kpbianco/gr86-cca-telemetry/docs/engineering/rvb22/analyses/mated_i22/MATED_SERVICE_ENVELOPES.png

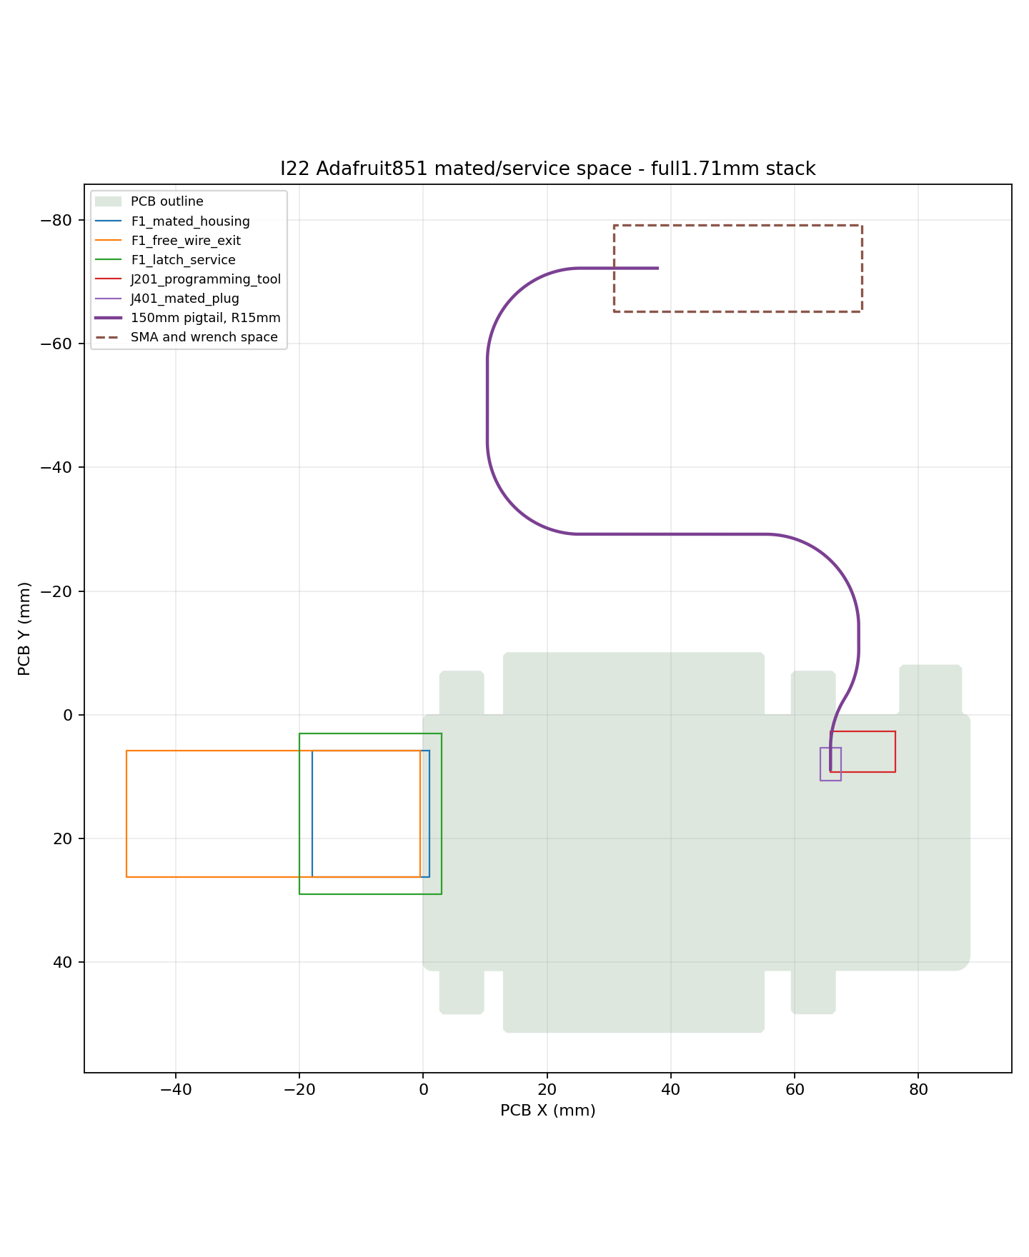
docs/engineering/rvb22/analyses/mated_i22/MATED_SERVICE_ENVELOPES.png
