kpbianco/gr86-cca-telemetry/docs/engineering/rvb22/candidate/cad/models/ENVELOPE_TI_DRB0008J_TCAN3403.step

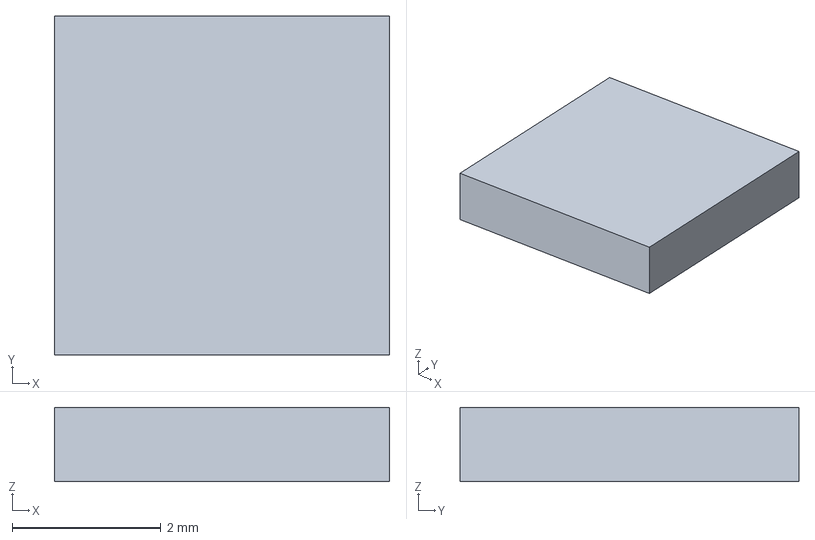
[picture p22: CAD file, 2026-09-10]
docs/engineering/rvb22/candidate/cad/models/ENVELOPE_TI_DRB0008J_TCAN3403.step
4.50 x 4.55 x 1.00 mm
