kpbianco/gr86-cca-telemetry/docs/engineering/rvb22/candidate/cad/models/ENVELOPE_TPS3808_DBV0006A.step

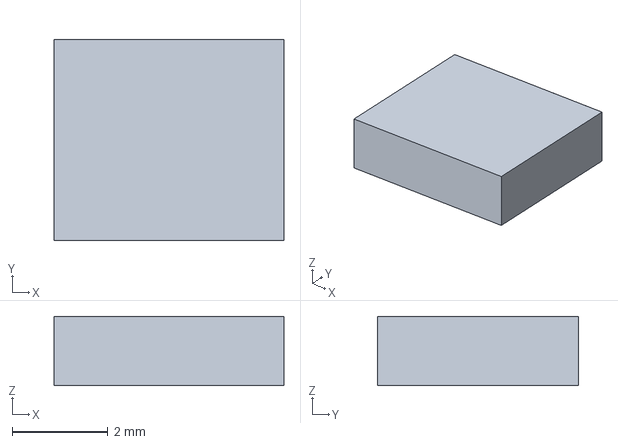
[picture p23: CAD file, 2026-09-10]
docs/engineering/rvb22/candidate/cad/models/ENVELOPE_TPS3808_DBV0006A.step
4.80 x 4.20 x 1.45 mm
