kpbianco/gr86-cca-telemetry/docs/engineering/rvb22/candidate/cad/models/ENVELOPE_TI_DDA0008B_4214849B.step

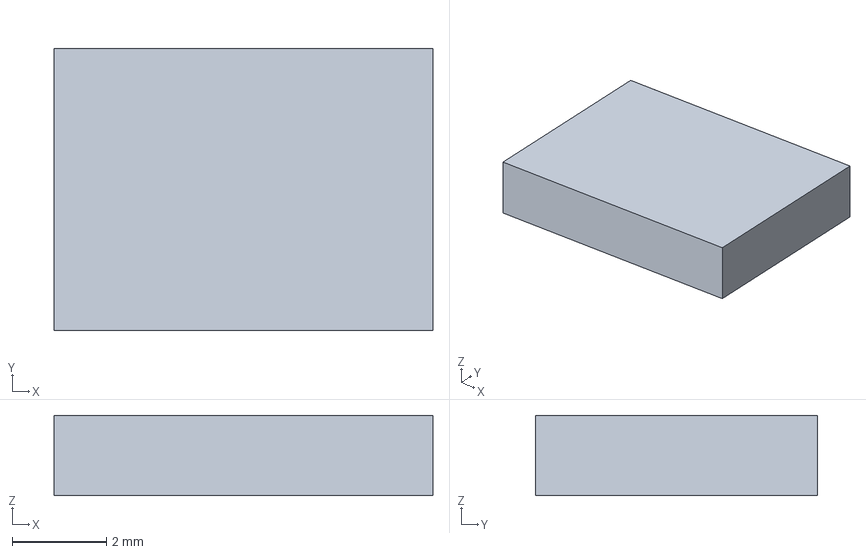
[picture p24: CAD file, 2026-09-10]
docs/engineering/rvb22/candidate/cad/models/ENVELOPE_TI_DDA0008B_4214849B.step
8.05 x 6.00 x 1.70 mm
