kpbianco/gr86-cca-telemetry/docs/engineering/rvb22/candidate/cad/models/ENVELOPE_WSLP0603_MANUFACTURER.step

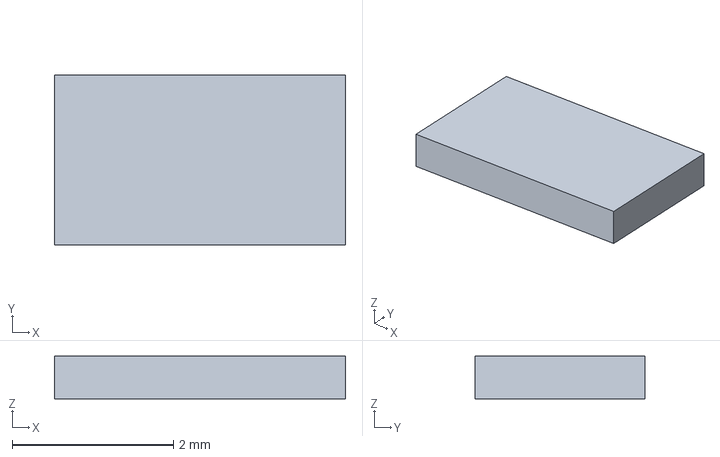
[picture p25: CAD file, 2026-09-10]
docs/engineering/rvb22/candidate/cad/models/ENVELOPE_WSLP0603_MANUFACTURER.step
3.61 x 2.11 x 0.533 mm
