kpbianco/gr86-cca-telemetry/docs/engineering/rvb22/candidate/mechanics/HARNESS_CORRIDORS_C03.scad

// Service and installed harness envelopes only; translucent volumes are not fabricated parts.
// Primary left: preserve twist, maximum6mm round bundle,≤1.3mmstrap; maxstack7.3mm.
color([0,0.4,1,.2])translate([-7.5,25,-16.3])cube([7,17,7.3]);
// Side parked T18R head volumes; do not put3.7mmheads beneath6mmbundle.
for(y=[31,37])color([0,0.8,1,.3])translate([-12.5,y-2.6,-12.9])cube([5.2,5.2,3.9]);
// Right coax service loop only; SMA bulkhead carries external coax pull.
for(y=[33,39]){
 color([0,.4,1,.2])translate([60.55,y-.8,-11.8])cube([3.9,1.6,2.8]);
 color([0,.8,1,.3])translate([59.9,y-2.6,-12.9])cube([5.2,5.2,3.9]);
}
