kpbianco/gr86-cca-telemetry/docs/engineering/rvb22/candidate/mechanics/MECH_GEOMETRY.scad

mounts=[[6.2, -4], [63, -4], [6.2, 45.28735489815251], [63, 45.263840607765246]];
outline=[[0.0, 0.980947], [0.0007564188822328788, 0.942435158452663], [0.003024212185312014, 0.9039827044031863], [0.006799883183623678, 0.8656489279468407], [0.01207761014488229, 0.8274929361891232], [0.018849255306698454, 0.78957356210812], [0.027104377424249204, 0.7519492738395437], [0.03683024786970257, 0.7146780845243252], [0.04801187025857423, 0.6778174628577655], [0.060632003572752335, 0.6414242444781693], [0.0746711887445386, 0.6055545443315986], [0.09010777866071418, 0.5702636701478605], [0.10691797154036797, 0.5356060371611512], [0.12507584763502144, 0.5016350842068436], [0.1445534091944619, 0.46840319132378905], [0.16532062363665956, 0.43596159898918896], [0.18734546985520617, 0.4043603291105594], [0.21059398759287262, 0.37364810789661906], [0.23503032980515604, 0.3438722907260233], [0.260616817933077, 0.3150787891297888], [0.287314, 0.287312], [0.3150803908230424, 0.26061490483005567], [0.3438735029496004, 0.23502850133291553], [0.3736489390329585, 0.21059224229236606], [0.4043607870385453, 0.1873438070346387], [0.43596169103768645, 0.16531904332902592], [0.468402924227763, 0.14455191211265295], [0.5016344640661801, 0.12507443512463678], [0.53560506940229, 0.10691664553038094], [0.5702623594883429, 0.09010654161213605], [0.6055528947476301, 0.07467004359723661], [0.641422259175283, 0.06063095369057858], [0.6778151442446667, 0.04801091937296942], [0.7146754341899937, 0.03682940002194035], [0.7519462925336527, 0.027103636906487982], [0.7895702497248368, 0.018848626602015806], [0.8274892917543318, 0.012077097866464714], [0.8656449496088303, 0.006799492013290109], [0.903978389426835, 0.0030239468115478285], [0.9424305032171397, 0.0007562839379161579], [0.980942, 0.0], [2.7, 0.0], [2.7, -6.5], [3.2, -7.0], [9.2, -7.0], [9.7, -6.5], [9.7, 0.0], [13.0, 0.0], [13.0, -9.5], [13.5, -10.0], [54.5, -10.0], [55.0, -9.5], [55.0, 0.0], [59.5, 0.0], [59.5, -6.5], [60.0, -7.0], [66.0, -7.0], [66.5, -6.5], [66.5, 0.0], [87.273825, 0.0], [87.279325, 0.000119], [87.31917532744609, 0.0026236857404802194], [87.35889700611345, 0.006686971610978976], [87.39842910058384, 0.012302624289232122], [87.43771096627245, 0.019462029029937433], [87.47668234246028, 0.02815420288028525], [87.51528344473775, 0.038365811528462634], [87.55345505671744, 0.05008118975928022], [87.59113862087561, 0.06328236548554456], [87.62827632838292, 0.07794908731830896], [87.66481120778663, 0.09405885563370964], [87.70068721240811, 0.11158695708872601], [87.73584930632194, 0.1305065025329204], [87.7702435487841, 0.15078846825799386], [87.80381717698043, 0.17240174052188162], [87.83651868696788, 0.19531316327908455], [87.86829791268461, 0.21948758904401522], [87.89910610290771, 0.2448879328093322], [87.92889599604048, 0.2714752289365473], [87.95762189261458, 0.2992086909316338], [87.98523972539566, 0.32804577401393376], [88.01170712698514, 0.3579422403823842], [88.03698349481435, 0.38885222707893363], [88.06103005343128, 0.4207283163450509], [88.0838099139844, 0.4535216083633855], [88.10528813081234, 0.48718179627299796], [88.1254317550527, 0.5216572433430767], [88.14420988518748, 0.5568950621867558], [88.16159371444789, 0.5928411958935125], [88.1775565750056, 0.629440500955684], [88.19207397888283, 0.6666368318618888], [88.20512365551836, 0.7043731272275816], [88.21668558593187, 0.7425914973306122], [88.2267420334342, 0.781233312917503], [88.23527757083666, 0.8202392951442118], [88.242279104117, 0.8595496065134053], [88.24773589250667, 0.8991039426687403], [88.2516395649676, 0.9388416249053337], [88.25398413303402, 0.9787016932545063], [88.254766, 1.018623], [88.254766, 38.837428], [88.25282560831081, 38.93625815706814], [88.24700661399163, 39.03493593760223], [88.23731798971754, 39.13330918409585], [88.22377467499068, 39.23122620862289], [88.20639755310395, 39.3285360267347], [88.1852134189399, 39.425088590272594], [88.16025493765383, 39.520735018736566], [88.13156059430547, 39.61532782885354], [88.09917463451636, 39.70872116199118], [88.06314699624474, 39.800771009066494], [88.02353323278307, 39.89133543260258], [87.9803944270969, 39.98027478559096], [87.93379709763715, 40.06745192682213], [87.88381309577116, 40.15273243235229], [87.83051949499047, 40.235984802780095], [87.77399847206637, 40.31708066601388], [87.71433718033633, 40.39589497521674], [87.65162761531678, 40.47230620162411], [87.58596647284935, 40.546196521936665], [87.517455, 40.617452], [87.45586352761268, 40.67667108709577], [87.39199461067004, 40.733426449801584], [87.32594673031547, 40.787630575548256], [87.25782172749265, 40.83919988558521], [87.18772464591447, 40.88805486385268], [87.11576357009325, 40.93412017958964], [87.0420494586825, 40.97732480348823], [86.96669597338692, 41.0176021172157], [86.88981930370436, 41.05489001613497], [86.81153798777032, 41.08913100506534], [86.73197272958086, 41.12027228693585], [86.65124621287598, 41.14826584419443], [86.56948291197034, 41.1730685128474], [86.48680889982317, 41.194642049015215], [86.403351653643, 41.21295318790161], [86.3192398583273, 41.227973695085524], [86.23460320803983, 41.23968041005645], [86.14957220623191, 41.24805528192625], [86.0642779644157, 41.25308539726227], [85.978852, 41.254763], [84.927437, 41.254763], [66.5, 41.262391664], [66.5, 47.763840608], [66.0, 48.263840608], [60.0, 48.263840608], [59.5, 47.763840608], [59.5, 41.265289552], [55.0, 41.26715248], [55.0, 50.775846143], [54.5, 51.275846143], [13.5, 51.275846143], [13.0, 50.775846143], [13.0, 41.284539807], [9.7, 41.285905954], [9.7, 47.787354898], [9.2, 48.287354898], [3.2, 48.287354898], [2.7, 47.787354898], [2.7, 41.288803842], [2.557101, 41.288863], [1.475399, 41.288863], [1.4122104655346492, 41.28762231281473], [1.3491193576042668, 41.28390178964085], [1.2862229598747368, 41.277707167358635], [1.2236182557775235, 41.269047997798516], [1.1614017789655595, 41.25793763301257], [1.0996694644626723, 41.24439320468623], [1.03851650073607, 41.22843559772205], [0.9780371829199807, 41.21008941803605], [0.9183247674167766, 41.18938295461655], [0.8594713280997736, 41.16634813590377], [0.8015676143394357, 41.14102048055766], [0.7447029110719076, 41.113439042689656], [0.6889649011256369, 41.083646351643026], [0.634439530018376, 41.05168834641451], [0.5812108734330366, 41.01761430481844], [0.5293610075767512, 40.98147676750257], [0.47896988262303, 40.94333145693274], [0.4301151994321739, 40.90323719147131], [0.3828722897400214, 40.8612557946819], [0.337314, 40.817452], [0.305970845153, 40.78485295628958], [0.2759316730593214, 40.75104853133481], [0.24724280095893103, 40.716090847999034], [0.2199484640714049, 40.6800338073486], [0.19409074738987742, 40.64293300554305], [0.169709520790415, 40.60484564811171], [0.14684237755686635, 40.565830461748796], [0.1255245764159767, 40.52594760376301], [0.10578898717214313, 40.48525856932134], [0.08766604002564038, 40.44382609662996], [0.0711836786524549, 40.40171407019854], [0.05636731711807896, 40.35898742233705], [0.043239800691699415, 40.315712033036995], [0.03182137062119672, 40.271954628391356], [0.022129632923273412, 40.22778267771005], [0.01417953123683069, 40.183264289489316], [0.007983323781449947, 40.13846810639559], [0.003550564456509253, 40.09346319942575], [0.0008880881100770122, 40.04831896140691], [0.0, 40.003105], [0.0, 37.820272], [2e-06, 2.834492], [0.0, 0.980947]];
