kpbianco/gr86-cca-telemetry/docs/engineering/rvb22/candidate/mechanics/THERMAL_CONTACT_T01.scad

// T01 thermal correction candidate, PCB bottomZ0. Package/copper heat-flow execution gate remains.
$fn=64;
// Copper packet is a volume envelope only:40 unbonded C110 laminae, each0.050..0.055mm.
module foil_packet(){translate([0,28.8,0])rotate([90,0,0])linear_extrude(17)polygon(points=[[68.36742356920699, -2.327], [66.6, -2.327], [66.6, -0.127], [72.0, -0.127], [72.10781885436252, -0.13229680066058358], [72.21459935421774, -0.14813619155644653], [72.31931314497992, -0.17436563069457023], [72.4209517756016, -0.21073251423758466], [72.5185364105086, -0.2568866092168096], [72.61112725632157, -0.3123834264672003], [72.69783261258002, -0.3766885013009893], [72.7778174593052, -0.4491825406947978], [72.85031149869901, -0.52916738741999], [72.9146165735328, -0.6158727436784377], [72.9701133907832, -0.7084635894914025], [73.01626748576241, -0.8060482243984013], [73.05263436930542, -0.9076868550200916], [73.07886380844356, -1.012400645782259], [73.09470319933942, -1.1191811456374834], [73.1, -1.227], [73.09487815202365, -1.3330275069087165], [73.07956030505223, -1.438067637868891], [73.05418910578301, -1.5411422118219895], [73.01900082226263, -1.6412913518625305], [72.97432314365243, -1.7375824240446052], [72.92057212863925, -1.8291187224896746], [72.85824833090943, -1.9150478199160048], [72.78793213776713, -1.994569505825846], [72.71027836530604, -2.066943238426374], [72.62601016046679, -2.1314950408887503], [72.53591226676653, -2.187623777724227], [72.44082371641346, -2.234806752828848], [72.34163001686069, -2.2726045770652346], [72.23925490456152, -2.300665260052341], [72.13465174271914, -2.3187274880585806], [72.02879464313867, -2.326623057473113], [71.90058141754851, -2.32998043894255], [71.80143533452095, -2.3377834049017934], [71.70283350343949, -2.350764582230358], [71.60504618506926, -2.3688883904235123], [71.5083414076529, -2.3921051533827487], [71.41298423226331, -2.420351235574614], [71.31923602629023, -2.4535492164511146], [71.22735374704972, -2.4916081026542893], [71.13758923748254, -2.534423577422475], [71.05018853586998, -2.581878286515418], [70.96539120145998, -2.6338421598740327], [70.88342965785215, -2.69017276813329], [70.8045285559402, -2.750715713011612], [70.72890415816008, -2.8153050505054087], [70.6567637457299, -2.883763745729839], [70.58830505050534, -2.955904158160167], [70.52371571301163, -3.031528555940172], [70.4631727681333, -3.1104296578521233], [70.40684215987407, -3.1923912014599107], [70.35487828651533, -3.2771885358701187], [70.30742357742251, -3.3645892374824644], [70.26460810265428, -3.454353747049748], [70.22654921645118, -3.5462360262900696], [70.19335123557458, -3.639984232263409], [70.16510515338277, -3.735341407652838], [70.1418883904235, -3.8320461850692933], [70.12376458223035, -3.9298335034395655], [70.11078340490178, -4.028435334520958], [70.10298043894254, -4.127581417548563], [70.1, -4.241399788793378], [70.1, -9.227], [70.09962305747311, -9.25579464313863], [70.09551166173684, -9.412802511867461], [70.09249767137017, -9.470312874029457], [70.08017475321127, -9.626890395103587], [70.07415503361601, -9.684164201245066], [70.0536543692966, -9.839882206562798], [70.04464542010577, -9.896762473162042], [70.01602320052177, -10.051194150494627], [70.00404971463885, -10.107524972694822], [69.96738439130463, -10.260247035549106], [69.95247918722222, -10.315874014481835], [69.90787125724049, -10.466467862299114], [69.89007518908686, -10.521238528281998], [69.837646919693, -10.669291393793058], [69.81700876525404, -10.723055624237448], [69.75690385869025, -10.868161704828948], [69.73348018571265, -10.920772135716533], [69.66586338534995, -11.062533705707772], [69.63971839649325, -11.113846135504243], [69.56477503528146, -11.251874636285603], [69.53598039214282, -11.301748421187552], [69.45391588462577, -11.435665526232635], [69.4225505113205, -11.483963965662385], [69.33358979060907, -11.613402617494723], [69.2997396574452, -11.659993328787014], [69.20412655869127, -11.784598745059107], [69.16788444653096, -11.829354026312698], [69.06588103859224, -11.948784672239759], [69.0273462845457, -11.991581852339715], [68.91923215167316, -12.105510376822783], [68.87851037682276, -12.146232151673171], [68.76458185233969, -12.254346284545711], [68.72178467223976, -12.292881038592228], [68.6023540263127, -12.394884446530959], [68.55759874505911, -12.431126558691263], [68.43299332878702, -12.526739657445193], [68.38640261749475, -12.560589790609049], [68.25696396566242, -12.649550511320477], [68.20866552623262, -12.680915884625781], [68.07474842118754, -12.762980392142826], [68.02487463628556, -12.79177503528148], [67.8868461355042, -12.866718396493267], [67.83553370570775, -12.892863385349957], [67.6937721357165, -12.960480185712656], [67.64116170482902, -12.983903858690207], [67.49605562423753, -13.04400876525401], [67.44229139379304, -13.064646919693004], [67.29423852828198, -13.11707518908686], [67.23946786229916, -13.134871257240471], [67.08887401448189, -13.179479187222215], [67.03324703554904, -13.194384391304654], [66.88052497269474, -13.231049714638866], [66.82419415049463, -13.243023200521767], [66.66976247316205, -13.271645420105763], [66.61288220656276, -13.280654369296604], [66.45716420124504, -13.301155033616011], [66.3998903951036, -13.30717475321126], [66.24331287402946, -13.319497671370163], [66.18580251186748, -13.322511661736836], [66.02879464313865, -13.326623057473114], [66.0, -13.327], [58.0, -13.327], [58.0, -11.127], [65.98560021120666, -11.127], [66.09941858245152, -11.12401956105745], [66.198564665479, -11.116216595098212], [66.29716649656054, -11.103235417769637], [66.39495381493076, -11.085111609576485], [66.49165859234711, -11.061894846617248], [66.58701576773667, -11.033648764425392], [66.68076397370979, -11.000450783548882], [66.77264625295031, -10.962391897345704], [66.8624107625175, -10.919576422577503], [66.94981146412995, -10.87212171348463], [67.03460879853999, -10.820157840125988], [67.11657034214791, -10.763827231866665], [67.19547144405982, -10.703284286988378], [67.27109584183987, -10.638694949494633], [67.34323625427007, -10.570236254270185], [67.41169494949473, -10.49809584183977], [67.47628428698836, -10.422471444059855], [67.5368272318667, -10.343570342147883], [67.59315784012593, -10.26160879854008], [67.64512171348467, -10.176811464129878], [67.69257642257753, -10.089410762517462], [67.73539189734565, -9.99964625295044], [67.77345078354887, -9.907763973709809], [67.8066487644254, -9.814015767736626], [67.83489484661723, -9.718658592347161], [67.8581116095765, -9.621953814930702], [67.87623541776965, -9.524166496560431], [67.88921659509822, -9.425564665479046], [67.89701956105746, -9.326418582451439], [67.9, -9.212600211206624], [67.9, -4.227], [67.90037694252689, -4.19820535686137], [67.90448833826316, -4.041197488132539], [67.90750232862983, -3.983687125970544], [67.91982524678873, -3.827109604896414], [67.92584496638399, -3.7698357987549334], [67.9463456307034, -3.6141177934372015], [67.95535457989423, -3.5572375268379597], [67.98397679947823, -3.402805849505375], [67.99595028536115, -3.346475027305181], [68.03261560869537, -3.193752964450896], [68.04752081277778, -3.1381259855181667], [68.09212874275951, -2.9875321377008874], [68.10992481091314, -2.9327614717179973], [68.162353080307, -2.784708606206939], [68.182991234746, -2.730944375762471], [68.2430961413098, -2.58583829517097], [68.26651981428732, -2.53322786428355], [68.33413661465, -2.391466294292311], [68.36028160350675, -2.340153864495755], [68.36742356920699, -2.327]]);}
color([.8,.4,.1])foil_packet();
//8805 insulating adhesive plus existing PCB soldermask; copper shall never touch live copper/vias.
color([1,1,1,.6])translate([66.6,11.8,-.127])cube([5.4,17,.127]);
//Chassis landing:mechanically attached to vehicle heat path; two M3 holes are below the PCB.
color("silver")difference(){translate([51,4,-15.327])cube([15.5,31.8,2]);for(y=[7.5,32.3])translate([54,y,-16])cylinder(d=3.4,h=4);}
//Dashed/transparent view envelopes are not additional hardware.
color([1,0,0,.08])translate([88.254766,-1.025,-18])cube([6,48.05,38]);
