kpbianco/gr86-cca-telemetry/docs/engineering/rvb22/current/mechanics/GR86_RVB_CARRIER_C05.scad

// C05 PCB bottomZ0. Controlled planar base and upper-right support relieved toX65mm;6mm posts.
$fn=64;
module c04_base(){translate([0,0,-9])linear_extrude(3)polygon(points=[[-8.0, 40.0], [-7.0, 40.0], [-7.0, 42.5], [-13.0, 42.5], [-13.0, 55.0], [-7.0, 55.0], [-7.0, 58.0], [66.5, 58.0], [66.5, -15.0], [-7.0, -15.0], [-7.0, -12.0], [-13.0, -12.0], [-13.0, -1.0], [-7.0, -1.0], [-7.0, 28.0], [-8.0, 28.0], [57.96211621656134, 2.05412009558888], [57.985960359806526, 2.059937493610912], [58.00973131920903, 2.066047057910296], [58.0334255149498, 2.07244786840912], [58.05703937877011, 2.0791389611688684], [58.080569354508924, 2.086119328535582], [58.104011898638454, 2.0933879192916125], [58.12736348079778, 2.1009436388139267], [58.15062058432453, 2.1087853492389574], [58.17377970678444, 2.1169118696339586], [58.19683736049887, 2.1253219761748503], [58.21979007306998, 2.1340144023305223], [58.24263438790368, 2.142987839053569], [58.26536686473018, 2.1522409349774265], [58.287984080122094, 2.1617722966198842], [58.31048262800998, 2.1715804885929386], [58.33285912019527, 2.1816640338189552], [58.355110186860564, 2.192021413753113], [58.37723247707706, 2.2026510686120924], [58.39922265930921, 2.2135513976089696], [58.42107742191648, 2.224720759194292], [58.442793473651996, 2.23615747130329], [58.46436754415824, 2.247859811609187], [58.48579638445957, 2.2598260177825775], [58.50707676745144, 2.2720542877568266], [58.52820548838644, 2.2845427799994558], [58.549179365356935, 2.2972896137894696], [58.569995239774194, 2.3102928695005858], [58.59064997684409, 2.323550588890324], [58.6111404660392, 2.3370607753949093], [58.63146362156723, 2.3508213944299494], [58.65161638283569, 2.3648303736968326], [58.671595714912876, 2.3790856034948105], [58.69139860898487, 2.3935849370387103], [58.711022082808654, 2.4083261907822333], [58.730463181161255, 2.4233071447467873], [58.749718976284775, 2.4385255428558112], [58.76878656832729, 2.4539790932745262], [58.787663085779585, 2.469665468755082], [58.80634568590755, 2.4855823069870313], [58.824831555180346, 2.5017272109530815], [58.84311790969404, 2.5180977492900816], [58.8612019955909, 2.5346914566551746], [58.879081089474134, 2.551505834097066], [58.896752498817946, 2.568538349432363], [58.91421356237309, 2.585786437626905], [58.931461650567634, 2.603247501182054], [58.948494165902936, 2.6209189105258663], [58.965308543344825, 2.638798004409094], [58.981902250709915, 2.656882090305963], [58.99827278904692, 2.6751684448196564], [59.014417693012966, 2.6936543140924467], [59.03033453124492, 2.7123369142204172], [59.046020906725474, 2.731213431672709], [59.061474457144186, 2.7502810237152273], [59.076692855253214, 2.7695368188387466], [59.09167380921777, 2.7889779171913487], [59.10641506296129, 2.8086013910151335], [59.12091439650519, 2.8284042850871223], [59.13516962630317, 2.848383617164309], [59.14917860557005, 2.8685363784327738], [59.16293922460509, 2.8888595339607956], [59.17644941110968, 2.9093500231559073], [59.189707130499414, 2.9300047602258052], [59.20271038621053, 2.9508206346430623], [59.215457220000545, 2.971794511613557], [59.22794571224318, 2.9929232325485646], [59.24017398221742, 3.014203615540432], [59.25214018839081, 3.0356324558417542], [59.26384252869671, 3.0572065263480046], [59.27527924080571, 3.07892257808352], [59.28644860239103, 3.100777340690787], [59.29734893138791, 3.1227675229229446], [59.30797858624689, 3.144889813139436], [59.318335966181046, 3.1671408798047254], [59.32841951140706, 3.1895173719900205], [59.33822770338011, 3.2120159198779037], [59.34775906502257, 3.2346331352698203], [59.35701216094643, 3.257365612096325], [59.36598559766948, 3.2802099269300236], [59.37467802382515, 3.303162639501131], [59.38308813036604, 3.32622029321556], [59.39121465076104, 3.3493794156754744], [59.39905636118608, 3.372636519202217], [59.406612080708385, 3.3959881013615436], [59.41388067146442, 3.4194306454910754], [59.420861038831134, 3.442960621229894], [59.42755213159088, 3.466574485050203], [59.433952942089704, 3.4902686807909706], [59.44006250638909, 3.514039640193472], [59.44587990441112, 3.537883783438658], [59.451404260077055, 3.5617975196862606], [59.45663474143925, 3.585777247615563], [59.461570560806464, 3.6098193559677436], [59.466210974862435, 3.633920224089718], [59.47055528477788, 3.6580762224793975], [59.47460283631572, 3.682283713332277], [59.478353019929564, 3.7065390510892766], [59.48180527085556, 3.7308385829857476], [59.48495906919742, 3.7551786496015676], [59.48781394000471, 3.7795555854122336], [59.49036945334439, 3.8039657193408787], [59.492625224365554, 3.8284053753111205], [59.49458091335738, 3.8528708728006653], [59.496236225800295, 3.877358527395583], [59.497590912410345, 3.901864651345164], [59.4986447691767, 3.926385554117282], [59.499397637392406, 3.9509175429541754], [59.49984940367829, 3.97545692342856], [59.5, 4.0], [59.5, 30.0], [58.5, 30.0], [58.5, 38.73201220968235], [58.48579638445957, 38.74017398221742], [58.46436754415824, 38.75214018839081], [58.442793473651996, 38.76384252869671], [58.42107742191648, 38.77527924080571], [58.39922265930921, 38.78644860239103], [58.37723247707706, 38.79734893138791], [58.355110186860564, 38.80797858624689], [58.33285912019527, 38.818335966181046], [58.31048262800998, 38.82841951140706], [58.287984080122094, 38.83822770338011], [58.26536686473018, 38.84775906502257], [58.24263438790368, 38.85701216094643], [58.21979007306998, 38.86598559766948], [58.19683736049887, 38.87467802382515], [58.17377970678444, 38.88308813036604], [58.15062058432453, 38.89121465076104], [58.12736348079778, 38.89905636118608], [58.104011898638454, 38.906612080708385], [58.080569354508924, 38.91388067146442], [58.05703937877011, 38.920861038831134], [58.0334255149498, 38.92755213159088], [58.00973131920903, 38.933952942089704], [57.985960359806526, 38.94006250638909], [57.96211621656134, 38.94587990441112], [57.93820248031374, 38.951404260077055], [57.91422275238444, 38.95663474143925], [57.890180644032256, 38.961570560806464], [57.86607977591028, 38.966210974862435], [57.841923777520606, 38.97055528477788], [57.817716286667725, 38.97460283631572], [57.79346094891072, 38.978353019929564], [57.76916141701425, 38.98180527085556], [57.74482135039843, 38.98495906919742], [57.72044441458777, 38.98781394000471], [57.69603428065912, 38.99036945334439], [57.67159462468888, 38.992625224365554], [57.647129127199335, 38.99458091335738], [57.622641472604414, 38.996236225800295], [57.598135348654836, 38.997590912410345], [57.57361444588272, 38.9986447691767], [57.54908245704583, 38.999397637392406], [57.52454307657144, 38.99984940367829], [57.5, 39.0], [2.0, 39.0], [1.9754569234285604, 38.99984940367829], [1.9509175429541756, 38.999397637392406], [1.9263855541172823, 38.9986447691767], [1.901864651345164, 38.997590912410345], [1.8773585273955828, 38.996236225800295], [1.8528708728006653, 38.99458091335738], [1.8284053753111205, 38.992625224365554], [1.8039657193408787, 38.99036945334439], [1.7795555854122338, 38.98781394000471], [1.7551786496015678, 38.98495906919742], [1.7308385829857478, 38.98180527085556], [1.7065390510892766, 38.978353019929564], [1.6822837133322774, 38.97460283631572], [1.6580762224793975, 38.97055528477788], [1.6339202240897182, 38.966210974862435], [1.6098193559677436, 38.961570560806464], [1.5857772476155632, 38.95663474143925], [1.5617975196862606, 38.951404260077055], [1.5378837834386578, 38.94587990441112], [1.5140396401934724, 38.94006250638909], [1.490268680790971, 38.933952942089704], [1.4665744850502034, 38.92755213159088], [1.442960621229894, 38.920861038831134], [1.4194306454910757, 38.91388067146442], [1.3959881013615438, 38.906612080708385], [1.3726365192022172, 38.89905636118608], [1.3493794156754744, 38.89121465076104], [1.32622029321556, 38.88308813036604], [1.3031626395011306, 38.87467802382515], [1.2802099269300236, 38.86598559766948], [1.257365612096325, 38.85701216094643], [1.2346331352698205, 38.84775906502257], [1.2120159198779041, 38.83822770338011], [1.1895173719900205, 38.82841951140706], [1.167140879804726, 38.818335966181046], [1.1448898131394363, 38.80797858624689], [1.1227675229229452, 38.79734893138791], [1.1007773406907866, 38.78644860239103], [1.0789225780835199, 38.77527924080571], [1.0572065263480046, 38.76384252869671], [1.0356324558417547, 38.75214018839081], [1.0142036155404321, 38.74017398221742], [0.9929232325485651, 38.72794571224318], [0.9717945116135567, 38.715457220000545], [0.9508206346430625, 38.70271038621053], [0.9300047602258059, 38.689707130499414], [0.9093500231559069, 38.67644941110967], [0.8888595339607961, 38.66293922460509], [0.8685363784327735, 38.64917860557005], [0.8483836171643093, 38.63516962630317], [0.8284042850871223, 38.62091439650519], [0.8086013910151333, 38.60641506296129], [0.7889779171913491, 38.59167380921777], [0.7695368188387466, 38.576692855253214], [0.7502810237152275, 38.561474457144186], [0.7312134316727092, 38.546020906725474], [0.7123369142204174, 38.53033453124492], [0.6936543140924463, 38.514417693012966], [0.6751684448196569, 38.49827278904692], [0.6568820903059631, 38.481902250709915], [0.638798004409094, 38.465308543344825], [0.6209189105258661, 38.448494165902936], [0.6032475011820544, 38.431461650567634], [0.5857864376269051, 38.41421356237309], [0.5685383494323628, 38.396752498817946], [0.5515058340970664, 38.379081089474134], [0.5346914566551746, 38.3612019955909], [0.5180977492900822, 38.34311790969404], [0.5017272109530813, 38.324831555180346], [0.4855823069870313, 38.30634568590755], [0.4696654687550821, 38.287663085779585], [0.453979093274526, 38.26878656832729], [0.438525542855811, 38.249718976284775], [0.42330714474678754, 38.230463181161255], [0.4083261907822331, 38.211022082808654], [0.39358493703871034, 38.19139860898487], [0.3790856034948107, 38.171595714912876], [0.3648303736968328, 38.15161638283569], [0.35082139442994986, 38.13146362156723], [0.3370607753949093, 38.1111404660392], [0.3235505888903243, 38.09064997684409], [0.31029286950058577, 38.069995239774194], [0.2972896137894696, 38.049179365356935], [0.284542779999456, 38.02820548838644], [0.2720542877568266, 38.00707676745144], [0.2598260177825773, 37.98579638445957], [0.24785981160918702, 37.96436754415824], [0.23615747130329012, 37.942793473651996], [0.2247207591942919, 37.92107742191648], [0.21355139760896957, 37.89922265930922], [0.20265106861209214, 37.87723247707706], [0.19202141375311377, 37.855110186860564], [0.18166403381895524, 37.83285912019527], [0.17158048859293862, 37.81048262800998], [0.16177229661988446, 37.787984080122094], [0.15224093497742652, 37.76536686473018], [0.14298783905356904, 37.74263438790368], [0.1340144023305223, 37.71979007306998], [0.1253219761748503, 37.69683736049887], [0.11691186963395839, 37.67377970678444], [0.10878534923895766, 37.65062058432453], [0.10094363881392665, 37.62736348079778], [0.0933879192916125, 37.604011898638454], [0.08611932853558235, 37.580569354508924], [0.07913896116886843, 37.55703937877011], [0.07244786840912032, 37.5334255149498], [0.06604705791029586, 37.50973131920903], [0.05993749361091205, 37.485960359806526], [0.05412009558887987, 37.46211621656134], [0.04859573992294308, 37.43820248031374], [0.04336525856074469, 37.41422275238444], [0.03842943919353914, 37.390180644032256], [0.03378902513756743, 37.36607977591028], [0.029444715222117557, 37.341923777520606], [0.02539716368428313, 37.317716286667725], [0.02164698007043797, 37.29346094891072], [0.01819472914443998, 37.26916141701425], [0.015040930802580066, 37.24482135039843], [0.012186059995287879, 37.22044441458777], [0.009630546655606365, 37.19603428065912], [0.007374775634443997, 37.17159462468888], [0.005419086642619586, 37.147129127199335], [0.0037637741997016416, 37.12264147260442], [0.00240908758965519, 37.098135348654836], [0.0013552308233011345, 37.07361444588272], [0.0006023626075915001, 37.04908245704583], [0.00015059632171099402, 37.02454307657144], [0.0, 37.0], [0.0, 4.0], [0.00015059632171099402, 3.97545692342856], [0.0006023626075915001, 3.9509175429541754], [0.0013552308233009125, 3.9263855541172825], [0.00240908758965519, 3.9018646513451642], [0.0037637741997016416, 3.877358527395583], [0.005419086642619586, 3.8528708728006644], [0.007374775634443997, 3.8284053753111196], [0.009630546655606365, 3.8039657193408782], [0.012186059995287879, 3.7795555854122336], [0.015040930802580066, 3.755178649601567], [0.01819472914443998, 3.7308385829857476], [0.02164698007043797, 3.706539051089276], [0.02539716368428313, 3.682283713332277], [0.029444715222117557, 3.6580762224793975], [0.03378902513756743, 3.633920224089718], [0.03842943919353914, 3.6098193559677427], [0.04336525856074491, 3.5857772476155625], [0.04859573992294308, 3.5617975196862597], [0.05412009558887987, 3.5378837834386574], [0.05993749361091205, 3.514039640193472], [0.06604705791029586, 3.4902686807909706], [0.07244786840912032, 3.466574485050203], [0.07913896116886843, 3.4429606212298935], [0.08611932853558235, 3.419430645491075], [0.09338791929161228, 3.395988101361544], [0.10094363881392665, 3.372636519202217], [0.10878534923895766, 3.3493794156754735], [0.11691186963395861, 3.3262202932155596], [0.1253219761748503, 3.3031626395011306], [0.1340144023305223, 3.2802099269300236], [0.14298783905356904, 3.257365612096325], [0.15224093497742652, 3.2346331352698203], [0.16177229661988446, 3.2120159198779037], [0.17158048859293862, 3.18951737199002], [0.18166403381895524, 3.167140879804726], [0.19202141375311332, 3.144889813139436], [0.20265106861209214, 3.122767522922945], [0.21355139760896957, 3.100777340690786], [0.22472075919429235, 3.0789225780835197], [0.23615747130329012, 3.057206526348004], [0.24785981160918702, 3.0356324558417542], [0.2598260177825773, 3.0142036155404317], [0.2720542877568266, 2.9929232325485646], [0.284542779999456, 2.9717945116135565], [0.2972896137894696, 2.950820634643062], [0.31029286950058577, 2.9300047602258057], [0.3235505888903243, 2.9093500231559064], [0.3370607753949093, 2.8888595339607956], [0.35082139442994986, 2.868536378432773], [0.3648303736968328, 2.848383617164309], [0.3790856034948107, 2.828404285087122], [0.39358493703871034, 2.808601391015133], [0.4083261907822331, 2.7889779171913487], [0.42330714474678754, 2.769536818838746], [0.438525542855811, 2.7502810237152273], [0.453979093274526, 2.731213431672709], [0.4696654687550821, 2.7123369142204172], [0.4855823069870313, 2.693654314092446], [0.5017272109530813, 2.675168444819657], [0.5180977492900822, 2.656882090305963], [0.5346914566551746, 2.6387980044090935], [0.5515058340970664, 2.620918910525866], [0.5685383494323628, 2.603247501182054], [0.5857864376269051, 2.585786437626905], [0.6032475011820544, 2.5685383494323624], [0.6209189105258661, 2.551505834097066], [0.638798004409094, 2.5346914566551746], [0.6568820903059631, 2.518097749290082], [0.6751684448196569, 2.5017272109530806], [0.6936543140924463, 2.4855823069870313], [0.7123369142204174, 2.469665468755082], [0.7312134316727092, 2.453979093274526], [0.7502810237152275, 2.438525542855811], [0.7695368188387466, 2.4233071447467873], [0.7889779171913491, 2.408326190782233], [0.8086013910151333, 2.3935849370387103], [0.8284042850871223, 2.3790856034948105], [0.8483836171643093, 2.3648303736968326], [0.8685363784327735, 2.35082139442995], [0.8888595339607961, 2.3370607753949093], [0.9093500231559069, 2.323550588890324], [0.9300047602258059, 2.3102928695005858], [0.9508206346430625, 2.2972896137894696], [0.9717945116135567, 2.2845427799994558], [0.9929232325485651, 2.272054287756826], [1.0142036155404321, 2.259826017782577], [1.0356324558417547, 2.247859811609187], [1.0572065263480046, 2.23615747130329], [1.0789225780835205, 2.224720759194292], [1.1007773406907866, 2.2135513976089696], [1.1227675229229452, 2.2026510686120924], [1.1448898131394354, 2.1920214137531135], [1.167140879804726, 2.1816640338189552], [1.1895173719900205, 2.1715804885929386], [1.2120159198779041, 2.1617722966198842], [1.2346331352698205, 2.1522409349774265], [1.257365612096325, 2.1429878390535686], [1.2802099269300236, 2.1340144023305223], [1.303162639501131, 2.12532197617485], [1.32622029321556, 2.1169118696339586], [1.3493794156754744, 2.108785349238957], [1.3726365192022172, 2.1009436388139267], [1.3959881013615438, 2.0933879192916125], [1.4194306454910757, 2.086119328535582], [1.442960621229894, 2.0791389611688684], [1.4665744850502034, 2.07244786840912], [1.490268680790971, 2.066047057910296], [1.5140396401934724, 2.059937493610912], [1.5378837834386578, 2.0541200955888796], [1.5617975196862606, 2.048595739922943], [1.5857772476155632, 2.043365258560745], [1.6098193559677436, 2.038429439193539], [1.6339202240897182, 2.033789025137567], [1.6580762224793975, 2.029444715222118], [1.6822837133322774, 2.025397163684283], [1.7065390510892766, 2.0216469800704377], [1.7308385829857478, 2.01819472914444], [1.7551786496015678, 2.01504093080258], [1.7795555854122338, 2.0121860599952877], [1.8039657193408787, 2.009630546655606], [1.8284053753111205, 2.007374775634444], [1.8528708728006653, 2.0054190866426196], [1.8773585273955828, 2.003763774199702], [1.901864651345164, 2.002409087589655], [1.9263855541172823, 2.001355230823301], [1.9509175429541756, 2.0006023626075917], [1.9754569234285604, 2.0001505963217108], [2.0, 2.0], [57.5, 2.0], [57.52454307657144, 2.0001505963217108], [57.54908245704583, 2.0006023626075917], [57.57361444588272, 2.001355230823301], [57.598135348654836, 2.002409087589655], [57.622641472604414, 2.003763774199702], [57.647129127199335, 2.0054190866426196], [57.67159462468888, 2.007374775634444], [57.69603428065912, 2.0096305466556066], [57.72044441458777, 2.0121860599952877], [57.74482135039843, 2.01504093080258], [57.76916141701425, 2.01819472914444], [57.79346094891072, 2.0216469800704377], [57.817716286667725, 2.025397163684283], [57.841923777520606, 2.029444715222118], [57.86607977591028, 2.033789025137567], [57.890180644032256, 2.038429439193539], [57.91422275238444, 2.043365258560745], [57.93820248031374, 2.048595739922943], [13.5, -0.5], [13.5, -1.5], [13.5, -8.5], [13.5, -12.5], [54.5, -12.5], [54.5, -8.5], [54.5, -1.5], [54.5, -0.5], [53.5, -0.5], [14.5, -0.5], [13.5, 42.8], [13.5, 41.8], [14.5, 41.8], [53.5, 41.8], [54.5, 41.8], [54.5, 42.8], [54.5, 49.8], [54.5, 54.5], [13.5, 54.5], [13.5, 49.8], [7.276149107791591, -3.7721774861885597], [7.273272343042382, -3.7589886358274427], [7.270233947426116, -3.745836080891262], [7.267034378513999, -3.7327218021064095], [7.263674118149337, -3.719647774435034], [7.260153672374984, -3.7066159667776115], [7.256473571357122, -3.693628341676441], [7.25263436930543, -3.6806868550200913], [7.248636644389613, -3.6677934557488485], [7.244480998652341, -3.6549500855612194], [7.240168057918574, -3.6421586786215103], [7.235698471701323, -3.629421161268558], [7.231072913103833, -3.6167394517256217], [7.226292078718213, -3.604115459811513], [7.221356688520538, -3.5915510866529785], [7.216267485762415, -3.5790482243984005], [7.211025236859063, -3.566608755932847], [7.205630731273883, -3.5542345545945104], [7.200084781399575, -3.541927483892599], [7.194388222435788, -3.529689397226689], [7.188541912263349, -3.5175221376076196], [7.182546731315067, -3.505427537379932], [7.17640358244314, -3.493407417945936], [7.17011339078319, -3.481463589491402], [7.163677103614948, -3.4695978507129652], [7.157095690219583, -3.4578119885472374], [7.150370141733745, -3.4461077779017097], [7.1435014710003, -3.434486981387456], [7.1364907124157915, -3.4229513490536836], [7.129338921774678, -3.411502618124193], [7.122047176110322, -3.4001425127357487], [7.1146165735328, -3.3888727436784376], [7.107048233063528, -3.377695008138025], [7.099343294466742, -3.36661098944037], [7.091502918077854, -3.355622356797917], [7.083528284628709, -3.3447307650583236], [7.075420595069772, -3.333937854455242], [7.067181070389267, -3.32324525036131], [7.0588109514293045, -3.312654563043375], [7.050311498699011, -3.3021673874199893], [7.041683992184705, -3.2917853028212294], [7.032929731157133, -3.281509872750845], [7.024050033975805, -3.2713426446508107], [7.015046237890455, -3.2612851496682795], [7.005919698839654, -3.2513389024250015], [6.996671791246613, -3.241505400789226], [6.987303907812201, -3.23178612565013], [6.977817459305203, -3.2221825406947975], [6.968213874349869, -3.212696092187799], [6.958494599210773, -3.203328208753386], [6.948661097574998, -3.1940803011603456], [6.938714850331721, -3.184953762109545], [6.928657355349189, -3.1759499660241945], [6.918490127249155, -3.167070268842867], [6.908214697178771, -3.1583160078152948], [6.89783261258001, -3.1496885013009894], [6.887345436956625, -3.1411890485706957], [6.87675474963869, -3.132818929610733], [6.866062145544758, -3.124579404930228], [6.855269234941677, -3.11647171537129], [6.844377643202083, -3.1084970819221454], [6.83338901055963, -3.1006567055332575], [6.822304991861975, -3.092951766936472], [6.811127256321562, -3.0853834264672], [6.799857487264251, -3.077952823889678], [6.788497381875807, -3.070661078225322], [6.777048650946316, -3.0635092875842083], [6.765513018612544, -3.0564985289997004], [6.7538922220982895, -3.049629858266255], [6.742188011452763, -3.0429043097804174], [6.730402149287035, -3.036322896385052], [6.718536410508597, -3.0298866092168093], [6.706592582054064, -3.0235964175568606], [6.6945724626200676, -3.017453268684933], [6.68247786239238, -3.0114580877366506], [6.670310602773311, -3.005611777564212], [6.658072516107401, -2.9999152186004254], [6.645765445405489, -2.9943692687261163], [6.633391244067153, -2.988974763140936], [6.620951775601599, -2.983732514237585], [6.608448913347021, -2.9786433114794626], [6.595884540188487, -2.973707921281787], [6.583260548274378, -2.9689270868961675], [6.570578838731442, -2.9643015282986767], [6.55784132137849, -2.9598319420814265], [6.54504991443878, -2.9555190013476595], [6.532206544251151, -2.9513633556103867], [6.519313144979908, -2.94736563069457], [6.506371658323559, -2.9435264286428775], [6.493384033222388, -2.939846327625016], [6.480352225564966, -2.9363258818506623], [6.467278197893591, -2.9329656214860016], [6.454163919108738, -2.929766052573884], [6.441011364172557, -2.9267276569576186], [6.42782251381144, -2.923850892208409], [6.414599354217741, -2.9211361915564464], [6.401343876750655, -2.918583963825662], [6.388058077636332, -2.9161945933721647], [6.374743957667247, -2.9139684400263555], [6.361403521900899, -2.9119058390387407], [6.348038779357839, -2.910007101029442], [6.334651742719137, -2.908272511941419], [6.321244428023271, -2.9067023329974084], [6.307818854362516, -2.905296800660583], [6.294377043578884, -2.9040561265989444], [6.280921019959634, -2.9029804976534406], [6.26745280993243, -2.902070075809836], [6.2539744417601595, -2.90132499817431], [6.240487945235495, -2.9007453769528153], [6.226995351375203, -2.9003312994341752], [6.2134986921142925, -2.900082827976941], [6.2, -2.9], [6.186501307885708, -2.900082827976941], [6.173004648624796, -2.9003312994341752], [6.159512054764505, -2.9007453769528153], [6.14602555823984, -2.90132499817431], [6.13254719006757, -2.902070075809836], [6.119078980040366, -2.9029804976534406], [6.105622956421116, -2.9040561265989444], [6.0921811456374835, -2.905296800660583], [6.078755571976728, -2.9067023329974084], [6.065348257280863, -2.908272511941419], [6.051961220642161, -2.910007101029442], [6.038596478099102, -2.9119058390387407], [6.025256042332752, -2.9139684400263555], [6.011941922363668, -2.9161945933721647], [5.998656123249345, -2.918583963825662], [5.985400645782259, -2.921136191556447], [5.97217748618856, -2.923850892208409], [5.958988635827443, -2.9267276569576186], [5.9458360808912625, -2.929766052573884], [5.93272180210641, -2.9329656214860016], [5.919647774435035, -2.936325881850663], [5.906615966777612, -2.939846327625016], [5.8936283416764415, -2.943526428642878], [5.880686855020091, -2.94736563069457], [5.867793455748849, -2.951363355610387], [5.854950085561219, -2.9555190013476595], [5.8421586786215105, -2.9598319420814265], [5.8294211612685585, -2.964301528298677], [5.8167394517256215, -2.9689270868961675], [5.804115459811514, -2.973707921281787], [5.791551086652978, -2.9786433114794626], [5.779048224398401, -2.983732514237585], [5.766608755932847, -2.9889747631409365], [5.754234554594511, -2.9943692687261163], [5.741927483892599, -2.9999152186004254], [5.729689397226689, -3.0056117775642126], [5.71752213760762, -3.0114580877366506], [5.705427537379933, -3.017453268684933], [5.693407417945936, -3.0235964175568606], [5.681463589491402, -3.0298866092168097], [5.669597850712965, -3.0363228963850526], [5.6578119885472375, -3.0429043097804174], [5.64610777790171, -3.049629858266255], [5.6344869813874565, -3.056498528999701], [5.622951349053684, -3.0635092875842087], [5.611502618124193, -3.070661078225322], [5.600142512735749, -3.077952823889678], [5.588872743678438, -3.0853834264672004], [5.577695008138026, -3.0929517669364723], [5.56661098944037, -3.1006567055332575], [5.555622356797917, -3.108497081922146], [5.544730765058324, -3.1164717153712904], [5.533937854455242, -3.1245794049302282], [5.52324525036131, -3.1328189296107336], [5.512654563043375, -3.141189048570696], [5.5021673874199895, -3.1496885013009894], [5.49178530282123, -3.158316007815295], [5.481509872750845, -3.1670702688428674], [5.471342644650811, -3.175949966024195], [5.46128514966828, -3.1849537621095454], [5.451338902425001, -3.194080301160346], [5.441505400789226, -3.2033282087533865], [5.43178612565013, -3.2126960921878], [5.422182540694798, -3.2221825406947975], [5.412696092187799, -3.23178612565013], [5.403328208753386, -3.2415054007892263], [5.394080301160346, -3.2513389024250015], [5.384953762109545, -3.2612851496682795], [5.375949966024195, -3.2713426446508107], [5.367070268842867, -3.2815098727508456], [5.358316007815295, -3.2917853028212294], [5.34968850130099, -3.30216738741999], [5.341189048570696, -3.3126545630433752], [5.332818929610733, -3.3232452503613104], [5.324579404930228, -3.333937854455242], [5.316471715371291, -3.3447307650583236], [5.3084970819221455, -3.3556223567979173], [5.3006567055332585, -3.36661098944037], [5.292951766936472, -3.3776950081380255], [5.2853834264672, -3.388872743678438], [5.277952823889678, -3.400142512735749], [5.270661078225322, -3.411502618124193], [5.263509287584208, -3.4229513490536845], [5.256498528999701, -3.4344869813874563], [5.249629858266255, -3.4461077779017106], [5.2429043097804175, -3.4578119885472374], [5.236322896385053, -3.4695978507129652], [5.22988660921681, -3.4814635894914026], [5.223596417556861, -3.493407417945936], [5.217453268684933, -3.5054275373799326], [5.21145808773665, -3.51752213760762], [5.205611777564212, -3.52968939722669], [5.199915218600426, -3.541927483892599], [5.194369268726116, -3.5542345545945113], [5.188974763140937, -3.5666087559328474], [5.183732514237585, -3.5790482243984014], [5.178643311479463, -3.591551086652979], [5.173707921281787, -3.604115459811513], [5.168927086896168, -3.616739451725622], [5.164301528298678, -3.629421161268558], [5.159831942081427, -3.6421586786215108], [5.15551900134766, -3.65495008556122], [5.151363355610387, -3.6677934557488494], [5.14736563069457, -3.6806868550200917], [5.143526428642877, -3.6936283416764417], [5.139846327625016, -3.706615966777612], [5.136325881850663, -3.719647774435034], [5.132965621486002, -3.73272180210641], [5.129766052573884, -3.745836080891262], [5.126727656957619, -3.758988635827443], [5.123850892208409, -3.7721774861885597], [5.121136191556447, -3.785400645782259], [5.118583963825662, -3.798656123249345], [5.116194593372165, -3.811941922363669], [5.113968440026356, -3.825256042332753], [5.111905839038741, -3.8385964780991024], [5.110007101029442, -3.851961220642161], [5.108272511941419, -3.8653482572808624], [5.106702332997409, -3.8787555719767286], [5.105296800660583, -3.8921811456374833], [5.104056126598945, -3.9056229564211162], [5.102980497653441, -3.9190789800403656], [5.102070075809836, -3.932547190067571], [5.10132499817431, -3.9460255582398407], [5.1007453769528155, -3.9595120547645055], [5.100331299434176, -3.9730046486247965], [5.100082827976941, -3.986501307885708], [5.1, -4.0], [5.100082827976941, -4.013498692114292], [5.100331299434176, -4.026995351375204], [5.1007453769528155, -4.040487945235495], [5.10132499817431, -4.05397444176016], [5.102070075809836, -4.067452809932429], [5.102980497653441, -4.080921019959635], [5.104056126598945, -4.094377043578884], [5.105296800660584, -4.107818854362517], [5.106702332997409, -4.121244428023272], [5.108272511941419, -4.134651742719138], [5.110007101029442, -4.148038779357839], [5.111905839038741, -4.161403521900898], [5.113968440026356, -4.174743957667248], [5.116194593372165, -4.188058077636331], [5.118583963825662, -4.201343876750655], [5.121136191556447, -4.214599354217741], [5.123850892208409, -4.227822513811441], [5.126727656957619, -4.241011364172557], [5.129766052573884, -4.254163919108739], [5.132965621486002, -4.2672781978935905], [5.136325881850663, -4.280352225564966], [5.139846327625016, -4.293384033222388], [5.143526428642877, -4.306371658323559], [5.14736563069457, -4.319313144979908], [5.151363355610387, -4.332206544251151], [5.15551900134766, -4.34504991443878], [5.159831942081427, -4.35784132137849], [5.164301528298678, -4.370578838731443], [5.168927086896168, -4.383260548274379], [5.173707921281787, -4.395884540188487], [5.178643311479463, -4.408448913347021], [5.183732514237585, -4.420951775601599], [5.188974763140937, -4.433391244067153], [5.194369268726116, -4.445765445405489], [5.199915218600426, -4.458072516107401], [5.205611777564212, -4.47031060277331], [5.21145808773665, -4.48247786239238], [5.217453268684933, -4.494572462620067], [5.223596417556861, -4.506592582054064], [5.22988660921681, -4.518536410508598], [5.236322896385053, -4.530402149287035], [5.2429043097804175, -4.542188011452763], [5.249629858266255, -4.553892222098289], [5.256498528999701, -4.565513018612544], [5.263509287584208, -4.577048650946316], [5.270661078225322, -4.588497381875807], [5.277952823889678, -4.599857487264251], [5.285383426467201, -4.611127256321563], [5.292951766936472, -4.6223049918619745], [5.3006567055332585, -4.63338901055963], [5.308497081922146, -4.644377643202083], [5.316471715371291, -4.655269234941677], [5.324579404930228, -4.666062145544759], [5.332818929610733, -4.67675474963869], [5.341189048570696, -4.687345436956625], [5.34968850130099, -4.69783261258001], [5.358316007815295, -4.708214697178771], [5.367070268842867, -4.718490127249154], [5.375949966024195, -4.728657355349189], [5.384953762109546, -4.7387148503317205], [5.394080301160346, -4.748661097574999], [5.403328208753386, -4.758494599210774], [5.4126960921878, -4.76821387434987], [5.422182540694798, -4.7778174593052025], [5.43178612565013, -4.7873039078122], [5.441505400789227, -4.796671791246614], [5.451338902425002, -4.805919698839654], [5.46128514966828, -4.815046237890455], [5.471342644650811, -4.824050033975805], [5.481509872750846, -4.832929731157133], [5.49178530282123, -4.841683992184705], [5.50216738741999, -4.850311498699011], [5.512654563043375, -4.858810951429304], [5.5232452503613105, -4.867181070389267], [5.5339378544552424, -4.875420595069772], [5.544730765058324, -4.883528284628709], [5.555622356797917, -4.891502918077855], [5.56661098944037, -4.8993432944667425], [5.577695008138026, -4.907048233063528], [5.588872743678438, -4.9146165735328005], [5.600142512735749, -4.922047176110322], [5.611502618124193, -4.929338921774678], [5.622951349053684, -4.936490712415791], [5.6344869813874565, -4.9435014710003], [5.646107777901711, -4.950370141733746], [5.6578119885472375, -4.957095690219583], [5.669597850712965, -4.963677103614947], [5.681463589491402, -4.97011339078319], [5.693407417945936, -4.976403582443139], [5.705427537379933, -4.982546731315066], [5.71752213760762, -4.988541912263349], [5.72968939722669, -4.994388222435788], [5.741927483892599, -5.000084781399575], [5.754234554594511, -5.005630731273884], [5.766608755932848, -5.011025236859064], [5.779048224398402, -5.016267485762415], [5.791551086652979, -5.021356688520537], [5.804115459811513, -5.026292078718213], [5.816739451725622, -5.0310729131038325], [5.8294211612685585, -5.035698471701323], [5.842158678621511, -5.0401680579185735], [5.85495008556122, -5.0444809986523405], [5.867793455748849, -5.048636644389614], [5.880686855020092, -5.05263436930543], [5.8936283416764415, -5.056473571357122], [5.906615966777612, -5.060153672374984], [5.919647774435035, -5.063674118149337], [5.93272180210641, -5.067034378513998], [5.945836080891262, -5.070233947426116], [5.958988635827444, -5.073272343042381], [5.97217748618856, -5.076149107791591], [5.985400645782259, -5.078863808443554], [5.998656123249345, -5.081416036174338], [6.011941922363669, -5.083805406627835], [6.025256042332753, -5.0860315599736445], [6.038596478099103, -5.088094160961259], [6.051961220642162, -5.089992898970558], [6.065348257280863, -5.091727488058581], [6.078755571976729, -5.093297667002592], [6.0921811456374835, -5.094703199339417], [6.105622956421117, -5.095943873401056], [6.119078980040366, -5.097019502346559], [6.132547190067571, -5.097929924190164], [6.14602555823984, -5.09867500182569], [6.159512054764505, -5.099254623047185], [6.173004648624797, -5.099668700565825], [6.186501307885709, -5.0999171720230585], [6.2, -5.1], [6.2134986921142925, -5.0999171720230585], [6.226995351375204, -5.099668700565825], [6.240487945235495, -5.099254623047185], [6.25397444176016, -5.09867500182569], [6.26745280993243, -5.097929924190164], [6.280921019959634, -5.097019502346559], [6.294377043578884, -5.095943873401056], [6.307818854362517, -5.094703199339417], [6.321244428023272, -5.093297667002592], [6.334651742719138, -5.091727488058581], [6.3480387793578394, -5.089992898970558], [6.361403521900898, -5.088094160961259], [6.374743957667247, -5.0860315599736445], [6.388058077636332, -5.083805406627835], [6.401343876750655, -5.081416036174338], [6.414599354217741, -5.078863808443554], [6.42782251381144, -5.076149107791591], [6.441011364172557, -5.073272343042381], [6.454163919108739, -5.070233947426116], [6.467278197893591, -5.067034378513998], [6.480352225564967, -5.063674118149337], [6.493384033222388, -5.060153672374984], [6.506371658323559, -5.056473571357122], [6.519313144979908, -5.05263436930543], [6.532206544251151, -5.048636644389613], [6.545049914438781, -5.0444809986523405], [6.55784132137849, -5.0401680579185735], [6.570578838731442, -5.035698471701323], [6.583260548274378, -5.0310729131038325], [6.595884540188488, -5.026292078718213], [6.608448913347021, -5.021356688520537], [6.620951775601599, -5.016267485762415], [6.633391244067153, -5.011025236859064], [6.645765445405489, -5.005630731273884], [6.658072516107401, -5.000084781399575], [6.670310602773311, -4.994388222435788], [6.682477862392381, -4.988541912263349], [6.6945724626200676, -4.982546731315067], [6.706592582054064, -4.976403582443139], [6.718536410508598, -4.97011339078319], [6.730402149287035, -4.963677103614947], [6.742188011452763, -4.957095690219583], [6.7538922220982895, -4.950370141733745], [6.765513018612544, -4.9435014710003], [6.777048650946316, -4.936490712415791], [6.788497381875807, -4.9293389217746775], [6.799857487264251, -4.922047176110322], [6.811127256321563, -4.9146165735328], [6.822304991861975, -4.907048233063528], [6.83338901055963, -4.8993432944667425], [6.844377643202083, -4.891502918077855], [6.855269234941677, -4.883528284628709], [6.866062145544758, -4.875420595069772], [6.87675474963869, -4.867181070389267], [6.887345436956625, -4.858810951429303], [6.89783261258001, -4.850311498699011], [6.908214697178771, -4.841683992184705], [6.918490127249155, -4.832929731157133], [6.9286573553491895, -4.824050033975805], [6.938714850331721, -4.815046237890455], [6.948661097574998, -4.805919698839654], [6.958494599210773, -4.796671791246614], [6.96821387434987, -4.7873039078122], [6.977817459305203, -4.7778174593052025], [6.9873039078122, -4.76821387434987], [6.996671791246614, -4.758494599210773], [7.005919698839654, -4.748661097574998], [7.015046237890456, -4.7387148503317205], [7.024050033975805, -4.728657355349189], [7.032929731157133, -4.718490127249154], [7.041683992184705, -4.708214697178771], [7.050311498699011, -4.69783261258001], [7.0588109514293045, -4.687345436956625], [7.0671810703892675, -4.67675474963869], [7.075420595069772, -4.666062145544759], [7.083528284628709, -4.655269234941676], [7.091502918077855, -4.644377643202083], [7.099343294466742, -4.63338901055963], [7.107048233063528, -4.6223049918619745], [7.1146165735328, -4.611127256321563], [7.122047176110322, -4.599857487264251], [7.1293389217746785, -4.588497381875807], [7.136490712415792, -4.577048650946316], [7.1435014710003, -4.565513018612544], [7.150370141733745, -4.553892222098289], [7.157095690219583, -4.542188011452763], [7.163677103614948, -4.530402149287035], [7.17011339078319, -4.518536410508597], [7.17640358244314, -4.506592582054064], [7.1825467313150675, -4.494572462620067], [7.188541912263349, -4.482477862392381], [7.194388222435788, -4.47031060277331], [7.200084781399575, -4.458072516107401], [7.205630731273884, -4.445765445405489], [7.211025236859063, -4.433391244067153], [7.216267485762415, -4.420951775601599], [7.221356688520538, -4.408448913347021], [7.226292078718213, -4.3958845401884865], [7.231072913103833, -4.383260548274378], [7.235698471701323, -4.370578838731442], [7.240168057918574, -4.357841321378489], [7.244480998652341, -4.345049914438781], [7.248636644389613, -4.332206544251151], [7.25263436930543, -4.319313144979908], [7.256473571357123, -4.306371658323559], [7.260153672374984, -4.293384033222388], [7.263674118149337, -4.280352225564966], [7.267034378513999, -4.2672781978935905], [7.270233947426116, -4.254163919108739], [7.273272343042382, -4.241011364172556], [7.276149107791591, -4.22782251381144], [7.278863808443553, -4.214599354217741], [7.281416036174338, -4.201343876750655], [7.2838054066278355, -4.188058077636331], [7.286031559973645, -4.174743957667248], [7.2880941609612595, -4.161403521900898], [7.289992898970558, -4.148038779357838], [7.291727488058581, -4.134651742719138], [7.293297667002592, -4.121244428023271], [7.294703199339417, -4.107818854362517], [7.295943873401056, -4.094377043578884], [7.29701950234656, -4.080921019959634], [7.297929924190164, -4.06745280993243], [7.29867500182569, -4.05397444176016], [7.299254623047185, -4.040487945235495], [7.2996687005658245, -4.026995351375204], [7.29991717202306, -4.013498692114292], [7.300000000000001, -4.0], [7.29991717202306, -3.9865013078857072], [7.2996687005658245, -3.9730046486247965], [7.299254623047185, -3.9595120547645046], [7.29867500182569, -3.9460255582398402], [7.297929924190164, -3.93254719006757], [7.29701950234656, -3.919078980040366], [7.295943873401056, -3.905622956421116], [7.294703199339417, -3.8921811456374833], [7.293297667002592, -3.878755571976728], [7.291727488058581, -3.8653482572808624], [7.289992898970558, -3.8519612206421607], [7.2880941609612595, -3.8385964780991015], [7.286031559973645, -3.8252560423327524], [7.2838054066278355, -3.811941922363668], [7.281416036174338, -3.7986561232493448], [7.278863808443553, -3.7854006457822584], [64.07886380844356, -3.7854006457822584], [64.0761491077916, -3.7721774861885597], [64.07327234304238, -3.7589886358274427], [64.07023394742612, -3.745836080891262], [64.067034378514, -3.7327218021064095], [64.06367411814934, -3.719647774435034], [64.06015367237498, -3.7066159667776115], [64.05647357135712, -3.693628341676441], [64.05263436930542, -3.6806868550200913], [64.04863664438962, -3.6677934557488485], [64.04448099865235, -3.6549500855612194], [64.04016805791858, -3.6421586786215103], [64.03569847170132, -3.629421161268558], [64.03107291310383, -3.6167394517256217], [64.02629207871821, -3.604115459811513], [64.02135668852054, -3.5915510866529785], [64.01626748576241, -3.5790482243984005], [64.01102523685907, -3.566608755932847], [64.00563073127388, -3.5542345545945104], [64.00008478139958, -3.541927483892599], [63.99438822243579, -3.529689397226689], [63.98854191226335, -3.5175221376076196], [63.98254673131507, -3.505427537379932], [63.97640358244314, -3.493407417945936], [63.97011339078319, -3.481463589491402], [63.96367710361495, -3.4695978507129652], [63.95709569021958, -3.4578119885472374], [63.95037014173374, -3.4461077779017097], [63.943501471000296, -3.434486981387456], [63.93649071241579, -3.4229513490536836], [63.92933892177468, -3.411502618124193], [63.92204717611032, -3.4001425127357487], [63.9146165735328, -3.3888727436784376], [63.90704823306353, -3.377695008138025], [63.89934329446674, -3.36661098944037], [63.891502918077855, -3.355622356797917], [63.88352828462871, -3.3447307650583236], [63.87542059506977, -3.333937854455242], [63.867181070389265, -3.32324525036131], [63.858810951429305, -3.312654563043375], [63.85031149869901, -3.3021673874199893], [63.841683992184706, -3.2917853028212294], [63.83292973115713, -3.281509872750845], [63.82405003397581, -3.2713426446508107], [63.815046237890456, -3.2612851496682795], [63.80591969883965, -3.2513389024250015], [63.79667179124662, -3.241505400789226], [63.7873039078122, -3.23178612565013], [63.777817459305204, -3.2221825406947975], [63.76821387434987, -3.212696092187799], [63.75849459921077, -3.203328208753386], [63.748661097574995, -3.1940803011603456], [63.73871485033172, -3.184953762109545], [63.72865735534919, -3.1759499660241945], [63.718490127249154, -3.167070268842867], [63.70821469717877, -3.1583160078152948], [63.69783261258001, -3.1496885013009894], [63.687345436956626, -3.1411890485706957], [63.67675474963869, -3.132818929610733], [63.66606214554476, -3.124579404930228], [63.65526923494168, -3.11647171537129], [63.644377643202084, -3.1084970819221454], [63.63338901055963, -3.1006567055332575], [63.622304991861974, -3.092951766936472], [63.61112725632156, -3.0853834264672], [63.59985748726425, -3.077952823889678], [63.588497381875804, -3.070661078225322], [63.57704865094632, -3.0635092875842083], [63.56551301861254, -3.0564985289997004], [63.55389222209829, -3.049629858266255], [63.542188011452765, -3.0429043097804174], [63.530402149287035, -3.036322896385052], [63.518536410508595, -3.0298866092168093], [63.50659258205406, -3.0235964175568606], [63.49457246262007, -3.017453268684933], [63.48247786239238, -3.0114580877366506], [63.47031060277331, -3.005611777564212], [63.4580725161074, -2.9999152186004254], [63.44576544540549, -2.9943692687261163], [63.43339124406715, -2.988974763140936], [63.4209517756016, -2.983732514237585], [63.40844891334702, -2.9786433114794626], [63.39588454018848, -2.973707921281787], [63.38326054827438, -2.9689270868961675], [63.37057883873144, -2.9643015282986767], [63.35784132137849, -2.9598319420814265], [63.34504991443878, -2.9555190013476595], [63.33220654425115, -2.9513633556103867], [63.31931314497991, -2.94736563069457], [63.306371658323556, -2.9435264286428775], [63.29338403322239, -2.939846327625016], [63.28035222556497, -2.9363258818506623], [63.26727819789359, -2.9329656214860016], [63.254163919108734, -2.929766052573884], [63.24101136417256, -2.9267276569576186], [63.22782251381144, -2.923850892208409], [63.21459935421774, -2.9211361915564464], [63.201343876750656, -2.918583963825662], [63.188058077636335, -2.9161945933721647], [63.174743957667246, -2.9139684400263555], [63.1614035219009, -2.9119058390387407], [63.14803877935784, -2.910007101029442], [63.134651742719136, -2.908272511941419], [63.121244428023275, -2.9067023329974084], [63.10781885436251, -2.905296800660583], [63.09437704357888, -2.9040561265989444], [63.08092101995963, -2.9029804976534406], [63.067452809932426, -2.902070075809836], [63.05397444176016, -2.90132499817431], [63.0404879452355, -2.9007453769528153], [63.026995351375206, -2.9003312994341752], [63.01349869211429, -2.900082827976941], [63.0, -2.9], [62.98650130788571, -2.900082827976941], [62.973004648624794, -2.9003312994341752], [62.9595120547645, -2.9007453769528153], [62.94602555823984, -2.90132499817431], [62.93254719006757, -2.902070075809836], [62.91907898004037, -2.9029804976534406], [62.90562295642111, -2.9040561265989444], [62.89218114563749, -2.905296800660583], [62.878755571976725, -2.9067023329974084], [62.865348257280864, -2.908272511941419], [62.85196122064216, -2.910007101029442], [62.8385964780991, -2.9119058390387407], [62.825256042332754, -2.9139684400263555], [62.811941922363665, -2.9161945933721647], [62.798656123249344, -2.918583963825662], [62.78540064578226, -2.921136191556447], [62.77217748618856, -2.923850892208409], [62.75898863582744, -2.9267276569576186], [62.74583608089126, -2.929766052573884], [62.73272180210641, -2.9329656214860016], [62.71964777443503, -2.936325881850663], [62.70661596677761, -2.939846327625016], [62.693628341676444, -2.943526428642878], [62.68068685502009, -2.94736563069457], [62.66779345574885, -2.951363355610387], [62.65495008556122, -2.9555190013476595], [62.64215867862151, -2.9598319420814265], [62.62942116126856, -2.964301528298677], [62.61673945172562, -2.9689270868961675], [62.60411545981151, -2.973707921281787], [62.59155108665298, -2.9786433114794626], [62.5790482243984, -2.983732514237585], [62.56660875593285, -2.9889747631409365], [62.55423455459451, -2.9943692687261163], [62.5419274838926, -2.9999152186004254], [62.52968939722669, -3.0056117775642126], [62.51752213760762, -3.0114580877366506], [62.50542753737993, -3.017453268684933], [62.49340741794594, -3.0235964175568606], [62.481463589491405, -3.0298866092168097], [62.469597850712965, -3.0363228963850526], [62.457811988547235, -3.0429043097804174], [62.44610777790171, -3.049629858266255], [62.43448698138746, -3.056498528999701], [62.42295134905368, -3.0635092875842087], [62.411502618124196, -3.070661078225322], [62.40014251273575, -3.077952823889678], [62.38887274367844, -3.0853834264672004], [62.377695008138026, -3.0929517669364723], [62.36661098944037, -3.1006567055332575], [62.355622356797916, -3.108497081922146], [62.34473076505832, -3.1164717153712904], [62.33393785445524, -3.1245794049302282], [62.32324525036131, -3.1328189296107336], [62.312654563043374, -3.141189048570696], [62.30216738741999, -3.1496885013009894], [62.29178530282123, -3.158316007815295], [62.281509872750846, -3.1670702688428674], [62.27134264465081, -3.175949966024195], [62.26128514966828, -3.1849537621095454], [62.251338902425005, -3.194080301160346], [62.24150540078923, -3.2033282087533865], [62.23178612565013, -3.2126960921878], [62.222182540694796, -3.2221825406947975], [62.2126960921878, -3.23178612565013], [62.20332820875338, -3.2415054007892263], [62.19408030116035, -3.2513389024250015], [62.184953762109544, -3.2612851496682795], [62.17594996602419, -3.2713426446508107], [62.16707026884286, -3.2815098727508456], [62.158316007815294, -3.2917853028212294], [62.149688501300986, -3.30216738741999], [62.141189048570695, -3.3126545630433752], [62.132818929610735, -3.3232452503613104], [62.12457940493023, -3.333937854455242], [62.11647171537129, -3.3447307650583236], [62.108497081922145, -3.3556223567979173], [62.10065670553326, -3.36661098944037], [62.09295176693647, -3.3776950081380255], [62.0853834264672, -3.388872743678438], [62.077952823889675, -3.400142512735749], [62.07066107822532, -3.411502618124193], [62.06350928758421, -3.4229513490536845], [62.056498528999704, -3.4344869813874563], [62.04962985826626, -3.4461077779017106], [62.04290430978042, -3.4578119885472374], [62.03632289638505, -3.4695978507129652], [62.02988660921681, -3.4814635894914026], [62.02359641755686, -3.493407417945936], [62.01745326868493, -3.5054275373799326], [62.01145808773665, -3.51752213760762], [62.00561177756421, -3.52968939722669], [61.99991521860043, -3.541927483892599], [61.99436926872612, -3.5542345545945113], [61.98897476314094, -3.5666087559328474], [61.98373251423759, -3.5790482243984014], [61.978643311479466, -3.591551086652979], [61.973707921281786, -3.604115459811513], [61.968927086896166, -3.616739451725622], [61.96430152829868, -3.629421161268558], [61.95983194208143, -3.6421586786215108], [61.95551900134766, -3.65495008556122], [61.95136335561039, -3.6677934557488494], [61.94736563069457, -3.6806868550200917], [61.943526428642876, -3.6936283416764417], [61.93984632762501, -3.706615966777612], [61.936325881850664, -3.719647774435034], [61.932965621486005, -3.73272180210641], [61.92976605257388, -3.745836080891262], [61.92672765695762, -3.758988635827443], [61.92385089220841, -3.7721774861885597], [61.92113619155645, -3.785400645782259], [61.91858396382566, -3.798656123249345], [61.91619459337216, -3.811941922363669], [61.91396844002636, -3.825256042332753], [61.91190583903874, -3.8385964780991024], [61.91000710102944, -3.851961220642161], [61.90827251194142, -3.8653482572808624], [61.906702332997405, -3.8787555719767286], [61.90529680066059, -3.8921811456374833], [61.904056126598945, -3.9056229564211162], [61.90298049765344, -3.9190789800403656], [61.90207007580984, -3.932547190067571], [61.90132499817431, -3.9460255582398407], [61.90074537695281, -3.9595120547645055], [61.90033129943418, -3.9730046486247965], [61.90008282797694, -3.986501307885708], [61.9, -4.0], [61.90008282797694, -4.013498692114292], [61.90033129943418, -4.026995351375204], [61.90074537695281, -4.040487945235495], [61.90132499817431, -4.05397444176016], [61.90207007580984, -4.067452809932429], [61.90298049765344, -4.080921019959635], [61.904056126598945, -4.094377043578884], [61.90529680066059, -4.107818854362517], [61.906702332997405, -4.121244428023272], [61.90827251194142, -4.134651742719138], [61.91000710102944, -4.148038779357839], [61.91190583903874, -4.161403521900898], [61.91396844002636, -4.174743957667248], [61.91619459337216, -4.188058077636331], [61.91858396382566, -4.201343876750655], [61.92113619155645, -4.214599354217741], [61.92385089220841, -4.227822513811441], [61.92672765695762, -4.241011364172557], [61.92976605257388, -4.254163919108739], [61.932965621486005, -4.2672781978935905], [61.936325881850664, -4.280352225564966], [61.93984632762502, -4.293384033222388], [61.943526428642876, -4.306371658323559], [61.94736563069457, -4.319313144979908], [61.95136335561039, -4.332206544251151], [61.95551900134766, -4.34504991443878], [61.95983194208143, -4.35784132137849], [61.96430152829868, -4.370578838731443], [61.968927086896166, -4.383260548274379], [61.973707921281786, -4.395884540188487], [61.978643311479466, -4.408448913347021], [61.98373251423759, -4.420951775601599], [61.98897476314094, -4.433391244067153], [61.99436926872612, -4.445765445405489], [61.99991521860043, -4.458072516107401], [62.00561177756421, -4.47031060277331], [62.01145808773665, -4.48247786239238], [62.01745326868493, -4.494572462620067], [62.02359641755686, -4.506592582054064], [62.02988660921681, -4.518536410508598], [62.03632289638505, -4.530402149287035], [62.04290430978042, -4.542188011452763], [62.04962985826626, -4.553892222098289], [62.056498528999704, -4.565513018612544], [62.06350928758421, -4.577048650946316], [62.07066107822532, -4.588497381875807], [62.077952823889675, -4.599857487264251], [62.0853834264672, -4.611127256321563], [62.09295176693647, -4.6223049918619745], [62.10065670553326, -4.63338901055963], [62.108497081922145, -4.644377643202083], [62.11647171537129, -4.655269234941677], [62.12457940493023, -4.666062145544759], [62.132818929610735, -4.67675474963869], [62.141189048570695, -4.687345436956625], [62.149688501300986, -4.69783261258001], [62.158316007815294, -4.708214697178771], [62.16707026884286, -4.718490127249154], [62.17594996602419, -4.728657355349189], [62.184953762109544, -4.7387148503317205], [62.19408030116035, -4.748661097574999], [62.20332820875338, -4.758494599210774], [62.2126960921878, -4.76821387434987], [62.222182540694796, -4.7778174593052025], [62.23178612565013, -4.7873039078122], [62.24150540078923, -4.796671791246614], [62.251338902425005, -4.805919698839654], [62.26128514966828, -4.815046237890455], [62.27134264465081, -4.824050033975805], [62.281509872750846, -4.832929731157133], [62.29178530282123, -4.841683992184705], [62.30216738741999, -4.850311498699011], [62.312654563043374, -4.858810951429304], [62.32324525036131, -4.867181070389267], [62.33393785445524, -4.875420595069772], [62.34473076505832, -4.883528284628709], [62.355622356797916, -4.891502918077855], [62.36661098944037, -4.8993432944667425], [62.377695008138026, -4.907048233063528], [62.38887274367844, -4.9146165735328005], [62.40014251273575, -4.922047176110322], [62.411502618124196, -4.929338921774678], [62.42295134905368, -4.936490712415791], [62.43448698138746, -4.9435014710003], [62.44610777790171, -4.950370141733746], [62.457811988547235, -4.957095690219583], [62.469597850712965, -4.963677103614947], [62.481463589491405, -4.97011339078319], [62.49340741794594, -4.976403582443139], [62.50542753737993, -4.982546731315066], [62.51752213760762, -4.988541912263349], [62.52968939722669, -4.994388222435788], [62.5419274838926, -5.000084781399575], [62.55423455459451, -5.005630731273884], [62.56660875593285, -5.011025236859064], [62.5790482243984, -5.016267485762415], [62.59155108665298, -5.021356688520537], [62.60411545981151, -5.026292078718213], [62.61673945172562, -5.0310729131038325], [62.62942116126856, -5.035698471701323], [62.64215867862151, -5.0401680579185735], [62.65495008556122, -5.0444809986523405], [62.66779345574885, -5.048636644389614], [62.68068685502009, -5.05263436930543], [62.693628341676444, -5.056473571357122], [62.70661596677761, -5.060153672374984], [62.71964777443503, -5.063674118149337], [62.73272180210641, -5.067034378513998], [62.74583608089126, -5.070233947426116], [62.75898863582744, -5.073272343042381], [62.77217748618856, -5.076149107791591], [62.78540064578226, -5.078863808443554], [62.798656123249344, -5.081416036174338], [62.811941922363665, -5.083805406627835], [62.825256042332754, -5.0860315599736445], [62.8385964780991, -5.088094160961259], [62.85196122064216, -5.089992898970558], [62.865348257280864, -5.091727488058581], [62.878755571976725, -5.093297667002592], [62.89218114563748, -5.094703199339417], [62.90562295642112, -5.095943873401056], [62.91907898004037, -5.097019502346559], [62.932547190067574, -5.097929924190164], [62.94602555823984, -5.09867500182569], [62.9595120547645, -5.099254623047185], [62.973004648624794, -5.099668700565825], [62.98650130788571, -5.0999171720230585], [63.0, -5.1], [63.01349869211429, -5.0999171720230585], [63.026995351375206, -5.099668700565825], [63.0404879452355, -5.099254623047185], [63.05397444176016, -5.09867500182569], [63.067452809932426, -5.097929924190164], [63.08092101995963, -5.097019502346559], [63.09437704357888, -5.095943873401056], [63.10781885436252, -5.094703199339417], [63.121244428023275, -5.093297667002592], [63.134651742719136, -5.091727488058581], [63.14803877935784, -5.089992898970558], [63.1614035219009, -5.088094160961259], [63.174743957667246, -5.0860315599736445], [63.188058077636335, -5.083805406627835], [63.201343876750656, -5.081416036174338], [63.21459935421774, -5.078863808443554], [63.22782251381144, -5.076149107791591], [63.24101136417256, -5.073272343042381], [63.25416391910874, -5.070233947426116], [63.26727819789359, -5.067034378513998], [63.28035222556497, -5.063674118149337], [63.29338403322239, -5.060153672374984], [63.306371658323556, -5.056473571357122], [63.31931314497991, -5.05263436930543], [63.33220654425115, -5.048636644389613], [63.34504991443878, -5.0444809986523405], [63.35784132137849, -5.0401680579185735], [63.37057883873144, -5.035698471701323], [63.38326054827438, -5.0310729131038325], [63.39588454018849, -5.026292078718213], [63.40844891334702, -5.021356688520537], [63.4209517756016, -5.016267485762415], [63.43339124406715, -5.011025236859064], [63.44576544540549, -5.005630731273884], [63.4580725161074, -5.000084781399575], [63.47031060277331, -4.994388222435788], [63.48247786239238, -4.988541912263349], [63.49457246262007, -4.982546731315067], [63.50659258205406, -4.976403582443139], [63.518536410508595, -4.97011339078319], [63.530402149287035, -4.963677103614947], [63.542188011452765, -4.957095690219583], [63.55389222209829, -4.950370141733745], [63.56551301861254, -4.9435014710003], [63.57704865094632, -4.936490712415791], [63.588497381875804, -4.9293389217746775], [63.59985748726425, -4.922047176110322], [63.61112725632156, -4.9146165735328], [63.622304991861974, -4.907048233063528], [63.63338901055963, -4.8993432944667425], [63.644377643202084, -4.891502918077855], [63.65526923494168, -4.883528284628709], [63.66606214554476, -4.875420595069772], [63.67675474963869, -4.867181070389267], [63.687345436956626, -4.858810951429303], [63.69783261258001, -4.850311498699011], [63.70821469717877, -4.841683992184705], [63.718490127249154, -4.832929731157133], [63.72865735534919, -4.824050033975805], [63.73871485033172, -4.815046237890455], [63.748661097574995, -4.805919698839654], [63.75849459921077, -4.796671791246614], [63.76821387434987, -4.7873039078122], [63.777817459305204, -4.7778174593052025], [63.7873039078122, -4.76821387434987], [63.79667179124662, -4.758494599210773], [63.80591969883965, -4.748661097574998], [63.815046237890456, -4.7387148503317205], [63.82405003397581, -4.728657355349189], [63.83292973115714, -4.718490127249154], [63.841683992184706, -4.708214697178771], [63.850311498699014, -4.69783261258001], [63.858810951429305, -4.687345436956625], [63.867181070389265, -4.67675474963869], [63.87542059506977, -4.666062145544759], [63.88352828462871, -4.655269234941676], [63.891502918077855, -4.644377643202083], [63.89934329446674, -4.63338901055963], [63.90704823306353, -4.6223049918619745], [63.9146165735328, -4.611127256321563], [63.922047176110325, -4.599857487264251], [63.92933892177468, -4.588497381875807], [63.93649071241579, -4.577048650946316], [63.943501471000296, -4.565513018612544], [63.95037014173374, -4.553892222098289], [63.95709569021958, -4.542188011452763], [63.96367710361495, -4.530402149287035], [63.97011339078319, -4.518536410508597], [63.97640358244314, -4.506592582054064], [63.98254673131507, -4.494572462620067], [63.98854191226335, -4.482477862392381], [63.99438822243579, -4.47031060277331], [64.00008478139958, -4.458072516107401], [64.00563073127388, -4.445765445405489], [64.01102523685907, -4.433391244067153], [64.01626748576241, -4.420951775601599], [64.02135668852054, -4.408448913347021], [64.02629207871821, -4.3958845401884865], [64.03107291310383, -4.383260548274378], [64.03569847170132, -4.370578838731442], [64.04016805791858, -4.357841321378489], [64.04448099865235, -4.345049914438781], [64.04863664438962, -4.332206544251151], [64.05263436930542, -4.319313144979908], [64.05647357135712, -4.306371658323559], [64.06015367237498, -4.293384033222388], [64.06367411814934, -4.280352225564966], [64.067034378514, -4.2672781978935905], [64.07023394742612, -4.254163919108739], [64.07327234304238, -4.241011364172556], [64.0761491077916, -4.22782251381144], [64.07886380844356, -4.214599354217741], [64.08141603617433, -4.201343876750655], [64.08380540662783, -4.188058077636331], [64.08603155997365, -4.174743957667248], [64.08809416096126, -4.161403521900898], [64.08999289897056, -4.148038779357838], [64.09172748805858, -4.134651742719138], [64.09329766700259, -4.121244428023271], [64.09470319933942, -4.107818854362517], [64.09594387340105, -4.094377043578884], [64.09701950234655, -4.080921019959634], [64.09792992419017, -4.06745280993243], [64.09867500182568, -4.05397444176016], [64.09925462304719, -4.040487945235495], [64.09966870056583, -4.026995351375204], [64.09991717202305, -4.013498692114292], [64.1, -4.0], [64.09991717202305, -3.9865013078857072], [64.09966870056583, -3.9730046486247965], [64.09925462304719, -3.9595120547645046], [64.09867500182568, -3.9460255582398402], [64.09792992419017, -3.93254719006757], [64.09701950234655, -3.919078980040366], [64.09594387340105, -3.905622956421116], [64.09470319933942, -3.8921811456374833], [64.09329766700259, -3.878755571976728], [64.09172748805858, -3.8653482572808624], [64.08999289897056, -3.8519612206421607], [64.08809416096126, -3.8385964780991015], [64.08603155997365, -3.8252560423327524], [64.08380540662783, -3.811941922363668], [64.08141603617433, -3.7986561232493448], [7.281416036174338, 45.48869877490316], [7.278863808443553, 45.50195425237025], [7.276149107791591, 45.51517741196395], [7.273272343042382, 45.528366262325065], [7.270233947426116, 45.54151881726125], [7.267034378513999, 45.554633096046096], [7.263674118149337, 45.567707123717476], [7.260153672374984, 45.580738931374896], [7.256473571357122, 45.593726556476064], [7.25263436930543, 45.606668043132416], [7.248636644389613, 45.61956144240366], [7.244480998652341, 45.63240481259129], [7.240168057918574, 45.645196219530995], [7.235698471701323, 45.65793373688395], [7.231072913103833, 45.670615446426886], [7.226292078718213, 45.683239438341], [7.221356688520538, 45.69580381149953], [7.216267485762415, 45.70830667375411], [7.211025236859063, 45.72074614221966], [7.205630731273883, 45.733120343558], [7.200084781399575, 45.74542741425991], [7.194388222435788, 45.75766550092582], [7.188541912263349, 45.76983276054489], [7.182546731315067, 45.78192736077258], [7.17640358244314, 45.79394748020657], [7.17011339078319, 45.8058913086611], [7.163677103614948, 45.81775704743954], [7.157095690219583, 45.82954290960527], [7.150370141733745, 45.8412471202508], [7.1435014710003, 45.85286791676505], [7.1364907124157915, 45.864403549098824], [7.129338921774678, 45.87585228002831], [7.122047176110322, 45.88721238541676], [7.1146165735328, 45.89848215447407], [7.107048233063528, 45.90965989001448], [7.099343294466742, 45.92074390871214], [7.091502918077854, 45.93173254135459], [7.083528284628709, 45.942624133094185], [7.075420595069772, 45.953417043697264], [7.067181070389267, 45.9641096477912], [7.0588109514293045, 45.974700335109134], [7.050311498699011, 45.985187510732516], [7.041683992184705, 45.995569595331276], [7.032929731157133, 46.00584502540166], [7.024050033975805, 46.0160122535017], [7.015046237890455, 46.026069748484225], [7.005919698839654, 46.0360159957275], [6.996671791246613, 46.04584949736328], [6.987303907812201, 46.055568772502376], [6.977817459305203, 46.06517235745771], [6.968213874349869, 46.07465880596471], [6.958494599210773, 46.084026689399124], [6.948661097574998, 46.09327459699216], [6.938714850331721, 46.102401136042964], [6.928657355349189, 46.111404932128316], [6.918490127249155, 46.12028462930964], [6.908214697178771, 46.12903889033721], [6.89783261258001, 46.13766639685152], [6.887345436956625, 46.14616584958181], [6.87675474963869, 46.15453596854177], [6.866062145544758, 46.16277549322228], [6.855269234941677, 46.17088318278122], [6.844377643202083, 46.17885781623036], [6.83338901055963, 46.18669819261925], [6.822304991861975, 46.194403131216035], [6.811127256321562, 46.201971471685304], [6.799857487264251, 46.209402074262826], [6.788497381875807, 46.21669381992719], [6.777048650946316, 46.2238456105683], [6.765513018612544, 46.230856369152804], [6.7538922220982895, 46.23772503988625], [6.742188011452763, 46.24445058837209], [6.730402149287035, 46.251032001767456], [6.718536410508597, 46.2574682889357], [6.706592582054064, 46.26375848059565], [6.6945724626200676, 46.269901629467576], [6.68247786239238, 46.27589681041586], [6.670310602773311, 46.281743120588295], [6.658072516107401, 46.28743967955208], [6.645765445405489, 46.29298562942639], [6.633391244067153, 46.29838013501157], [6.620951775601599, 46.30362238391492], [6.608448913347021, 46.30871158667304], [6.595884540188487, 46.31364697687072], [6.583260548274378, 46.31842781125634], [6.570578838731442, 46.32305336985383], [6.55784132137849, 46.32752295607108], [6.54504991443878, 46.33183589680485], [6.532206544251151, 46.33599154254212], [6.519313144979908, 46.33998926745794], [6.506371658323559, 46.34382846950963], [6.493384033222388, 46.347508570527495], [6.480352225564966, 46.351029016301844], [6.467278197893591, 46.35438927666651], [6.454163919108738, 46.357588845578626], [6.441011364172557, 46.36062724119489], [6.42782251381144, 46.3635040059441], [6.414599354217741, 46.36621870659606], [6.401343876750655, 46.36877093432685], [6.388058077636332, 46.37116030478035], [6.374743957667247, 46.37338645812615], [6.361403521900899, 46.37544905911377], [6.348038779357839, 46.377347797123065], [6.334651742719137, 46.37908238621109], [6.321244428023271, 46.3806525651551], [6.307818854362516, 46.38205809749192], [6.294377043578884, 46.38329877155356], [6.280921019959634, 46.38437440049907], [6.26745280993243, 46.38528482234267], [6.2539744417601595, 46.3860298999782], [6.240487945235495, 46.386609521199695], [6.226995351375203, 46.38702359871833], [6.2134986921142925, 46.38727207017557], [6.2, 46.38735489815251], [6.186501307885708, 46.38727207017557], [6.173004648624796, 46.38702359871833], [6.159512054764505, 46.386609521199695], [6.14602555823984, 46.3860298999782], [6.13254719006757, 46.38528482234267], [6.119078980040366, 46.38437440049907], [6.105622956421116, 46.38329877155356], [6.0921811456374835, 46.38205809749192], [6.078755571976728, 46.3806525651551], [6.065348257280863, 46.37908238621109], [6.051961220642161, 46.377347797123065], [6.038596478099102, 46.37544905911377], [6.025256042332752, 46.37338645812615], [6.011941922363668, 46.37116030478035], [5.998656123249345, 46.36877093432685], [5.985400645782259, 46.36621870659606], [5.97217748618856, 46.3635040059441], [5.958988635827443, 46.36062724119489], [5.9458360808912625, 46.357588845578626], [5.93272180210641, 46.35438927666651], [5.919647774435035, 46.351029016301844], [5.906615966777612, 46.347508570527495], [5.8936283416764415, 46.34382846950963], [5.880686855020091, 46.33998926745794], [5.867793455748849, 46.33599154254212], [5.854950085561219, 46.33183589680485], [5.8421586786215105, 46.32752295607108], [5.8294211612685585, 46.32305336985383], [5.8167394517256215, 46.31842781125634], [5.804115459811514, 46.31364697687072], [5.791551086652978, 46.30871158667304], [5.779048224398401, 46.30362238391492], [5.766608755932847, 46.29838013501157], [5.754234554594511, 46.29298562942639], [5.741927483892599, 46.28743967955208], [5.729689397226689, 46.281743120588295], [5.71752213760762, 46.27589681041586], [5.705427537379933, 46.269901629467576], [5.693407417945936, 46.26375848059565], [5.681463589491402, 46.2574682889357], [5.669597850712965, 46.251032001767456], [5.6578119885472375, 46.24445058837209], [5.64610777790171, 46.23772503988625], [5.6344869813874565, 46.230856369152804], [5.622951349053684, 46.2238456105683], [5.611502618124193, 46.21669381992719], [5.600142512735749, 46.209402074262826], [5.588872743678438, 46.201971471685304], [5.577695008138026, 46.194403131216035], [5.56661098944037, 46.18669819261925], [5.555622356797917, 46.17885781623036], [5.544730765058324, 46.17088318278122], [5.533937854455242, 46.16277549322228], [5.52324525036131, 46.15453596854177], [5.512654563043375, 46.14616584958181], [5.5021673874199895, 46.137666396851515], [5.49178530282123, 46.12903889033721], [5.481509872750845, 46.12028462930964], [5.471342644650811, 46.11140493212831], [5.46128514966828, 46.102401136042964], [5.451338902425001, 46.09327459699216], [5.441505400789226, 46.084026689399124], [5.43178612565013, 46.07465880596471], [5.422182540694798, 46.06517235745771], [5.412696092187799, 46.055568772502376], [5.403328208753386, 46.04584949736328], [5.394080301160346, 46.0360159957275], [5.384953762109545, 46.026069748484225], [5.375949966024195, 46.0160122535017], [5.367070268842867, 46.00584502540166], [5.358316007815295, 45.995569595331276], [5.34968850130099, 45.985187510732516], [5.341189048570696, 45.974700335109134], [5.332818929610733, 45.9641096477912], [5.324579404930228, 45.953417043697264], [5.316471715371291, 45.942624133094185], [5.3084970819221455, 45.93173254135459], [5.3006567055332585, 45.92074390871214], [5.292951766936472, 45.90965989001448], [5.2853834264672, 45.89848215447407], [5.277952823889678, 45.88721238541676], [5.270661078225322, 45.87585228002831], [5.263509287584208, 45.864403549098824], [5.256498528999701, 45.85286791676505], [5.249629858266255, 45.8412471202508], [5.2429043097804175, 45.82954290960527], [5.236322896385053, 45.81775704743954], [5.22988660921681, 45.8058913086611], [5.223596417556861, 45.79394748020657], [5.217453268684933, 45.78192736077258], [5.21145808773665, 45.76983276054489], [5.205611777564212, 45.75766550092582], [5.199915218600426, 45.74542741425991], [5.194369268726116, 45.733120343558], [5.188974763140937, 45.72074614221966], [5.183732514237585, 45.70830667375411], [5.178643311479463, 45.69580381149953], [5.173707921281787, 45.683239438341], [5.168927086896168, 45.670615446426886], [5.164301528298678, 45.65793373688395], [5.159831942081427, 45.645196219530995], [5.15551900134766, 45.63240481259129], [5.151363355610387, 45.61956144240366], [5.14736563069457, 45.606668043132416], [5.143526428642877, 45.593726556476064], [5.139846327625016, 45.580738931374896], [5.136325881850663, 45.567707123717476], [5.132965621486002, 45.554633096046096], [5.129766052573884, 45.54151881726125], [5.126727656957619, 45.528366262325065], [5.123850892208409, 45.51517741196395], [5.121136191556447, 45.50195425237025], [5.118583963825662, 45.48869877490316], [5.116194593372165, 45.47541297578884], [5.113968440026356, 45.462098855819754], [5.111905839038741, 45.44875842005341], [5.110007101029442, 45.43539367751035], [5.108272511941419, 45.42200664087164], [5.106702332997409, 45.40859932617578], [5.105296800660583, 45.39517375251502], [5.104056126598945, 45.38173194173139], [5.102980497653441, 45.36827591811214], [5.102070075809836, 45.354807708084934], [5.10132499817431, 45.34132933991267], [5.1007453769528155, 45.327842843388005], [5.100331299434176, 45.31435024952771], [5.100082827976941, 45.3008535902668], [5.1, 45.28735489815251], [5.100082827976941, 45.27385620603822], [5.100331299434176, 45.2603595467773], [5.1007453769528155, 45.24686695291701], [5.10132499817431, 45.23338045639235], [5.102070075809836, 45.21990208822008], [5.102980497653441, 45.206433878192875], [5.104056126598945, 45.19297785457363], [5.105296800660584, 45.17953604378999], [5.106702332997409, 45.16611047012923], [5.108272511941419, 45.15270315543337], [5.110007101029442, 45.13931611879467], [5.111905839038741, 45.12595137625161], [5.113968440026356, 45.11261094048526], [5.116194593372165, 45.09929682051617], [5.118583963825662, 45.08601102140185], [5.121136191556447, 45.07275554393477], [5.123850892208409, 45.05953238434107], [5.126727656957619, 45.04634353397995], [5.129766052573884, 45.033190979043766], [5.132965621486002, 45.02007670025892], [5.136325881850663, 45.00700267258754], [5.139846327625016, 44.99397086493012], [5.143526428642877, 44.98098323982895], [5.14736563069457, 44.9680417531726], [5.151363355610387, 44.95514835390136], [5.15551900134766, 44.942304983713726], [5.159831942081427, 44.92951357677402], [5.164301528298678, 44.91677605942107], [5.168927086896168, 44.90409434987813], [5.173707921281787, 44.89147035796402], [5.178643311479463, 44.878905984805485], [5.183732514237585, 44.866403122550906], [5.188974763140937, 44.853963654085355], [5.194369268726116, 44.841589452747016], [5.199915218600426, 44.82928238204511], [5.205611777564212, 44.8170442953792], [5.21145808773665, 44.80487703576013], [5.217453268684933, 44.79278243553244], [5.223596417556861, 44.780762316098446], [5.22988660921681, 44.76881848764391], [5.236322896385053, 44.75695274886547], [5.2429043097804175, 44.74516688669974], [5.249629858266255, 44.733462676054216], [5.256498528999701, 44.721841879539966], [5.263509287584208, 44.71030624720619], [5.270661078225322, 44.6988575162767], [5.277952823889678, 44.687497410888255], [5.285383426467201, 44.67622764183095], [5.292951766936472, 44.665049906290534], [5.3006567055332585, 44.653965887592875], [5.308497081922146, 44.642977254950424], [5.316471715371291, 44.63208566321083], [5.324579404930228, 44.62129275260775], [5.332818929610733, 44.61060014851382], [5.341189048570696, 44.60000946119588], [5.34968850130099, 44.5895222855725], [5.358316007815295, 44.57914020097374], [5.367070268842867, 44.56886477090335], [5.375949966024195, 44.558697542803316], [5.384953762109546, 44.54864004782079], [5.394080301160346, 44.53869380057751], [5.403328208753386, 44.52886029894174], [5.4126960921878, 44.51914102380264], [5.422182540694798, 44.5095374388473], [5.43178612565013, 44.500050990340306], [5.441505400789227, 44.49068310690589], [5.451338902425002, 44.481435199312855], [5.46128514966828, 44.47230866026205], [5.471342644650811, 44.4633048641767], [5.481509872750846, 44.45442516699537], [5.49178530282123, 44.4456709059678], [5.50216738741999, 44.43704339945349], [5.512654563043375, 44.4285439467232], [5.5232452503613105, 44.42017382776324], [5.5339378544552424, 44.41193430308274], [5.544730765058324, 44.4038266135238], [5.555622356797917, 44.39585198007465], [5.56661098944037, 44.38801160368577], [5.577695008138026, 44.38030666508898], [5.588872743678438, 44.37273832461971], [5.600142512735749, 44.36530772204218], [5.611502618124193, 44.35801597637783], [5.622951349053684, 44.35086418573672], [5.6344869813874565, 44.34385342715221], [5.646107777901711, 44.336984756418765], [5.6578119885472375, 44.330259207932926], [5.669597850712965, 44.32367779453756], [5.681463589491402, 44.31724150736932], [5.693407417945936, 44.31095131570937], [5.705427537379933, 44.30480816683744], [5.71752213760762, 44.29881298588916], [5.72968939722669, 44.29296667571672], [5.741927483892599, 44.287270116752936], [5.754234554594511, 44.281724166878625], [5.766608755932848, 44.276329661293445], [5.779048224398402, 44.271087412390095], [5.791551086652979, 44.265998209631974], [5.804115459811513, 44.261062819434294], [5.816739451725622, 44.25628198504867], [5.8294211612685585, 44.251656426451184], [5.842158678621511, 44.24718684023394], [5.85495008556122, 44.24287389950017], [5.867793455748849, 44.2387182537629], [5.880686855020092, 44.23472052884708], [5.8936283416764415, 44.230881326795384], [5.906615966777612, 44.22720122577752], [5.919647774435035, 44.22368078000317], [5.93272180210641, 44.220320519638506], [5.945836080891262, 44.21712095072639], [5.958988635827444, 44.214082555110124], [5.97217748618856, 44.211205790360914], [5.985400645782259, 44.20849108970896], [5.998656123249345, 44.20593886197817], [6.011941922363669, 44.20354949152467], [6.025256042332753, 44.20132333817887], [6.038596478099103, 44.199260737191246], [6.051961220642162, 44.19736199918195], [6.065348257280863, 44.19562741009393], [6.078755571976729, 44.19405723114991], [6.0921811456374835, 44.192651698813094], [6.105622956421117, 44.19141102475145], [6.119078980040366, 44.190335395805945], [6.132547190067571, 44.189424973962346], [6.14602555823984, 44.18867989632682], [6.159512054764505, 44.18810027510532], [6.173004648624797, 44.187686197586686], [6.186501307885709, 44.187437726129446], [6.2, 44.187354898152506], [6.2134986921142925, 44.187437726129446], [6.226995351375204, 44.187686197586686], [6.240487945235495, 44.18810027510532], [6.25397444176016, 44.18867989632682], [6.26745280993243, 44.189424973962346], [6.280921019959634, 44.190335395805945], [6.294377043578884, 44.19141102475145], [6.307818854362517, 44.192651698813094], [6.321244428023272, 44.19405723114991], [6.334651742719138, 44.19562741009393], [6.3480387793578394, 44.19736199918195], [6.361403521900898, 44.199260737191246], [6.374743957667247, 44.20132333817887], [6.388058077636332, 44.20354949152467], [6.401343876750655, 44.20593886197817], [6.414599354217741, 44.20849108970896], [6.42782251381144, 44.211205790360914], [6.441011364172557, 44.214082555110124], [6.454163919108739, 44.21712095072639], [6.467278197893591, 44.220320519638506], [6.480352225564967, 44.22368078000317], [6.493384033222388, 44.22720122577752], [6.506371658323559, 44.230881326795384], [6.519313144979908, 44.23472052884708], [6.532206544251151, 44.2387182537629], [6.545049914438781, 44.24287389950017], [6.55784132137849, 44.24718684023394], [6.570578838731442, 44.251656426451184], [6.583260548274378, 44.25628198504867], [6.595884540188488, 44.261062819434294], [6.608448913347021, 44.265998209631974], [6.620951775601599, 44.271087412390095], [6.633391244067153, 44.276329661293445], [6.645765445405489, 44.281724166878625], [6.658072516107401, 44.287270116752936], [6.670310602773311, 44.29296667571672], [6.682477862392381, 44.29881298588916], [6.6945724626200676, 44.30480816683744], [6.706592582054064, 44.31095131570937], [6.718536410508598, 44.31724150736932], [6.730402149287035, 44.32367779453756], [6.742188011452763, 44.330259207932926], [6.7538922220982895, 44.336984756418765], [6.765513018612544, 44.34385342715221], [6.777048650946316, 44.35086418573672], [6.788497381875807, 44.35801597637783], [6.799857487264251, 44.36530772204219], [6.811127256321563, 44.37273832461971], [6.822304991861975, 44.38030666508898], [6.83338901055963, 44.38801160368577], [6.844377643202083, 44.39585198007465], [6.855269234941677, 44.4038266135238], [6.866062145544758, 44.41193430308274], [6.87675474963869, 44.42017382776324], [6.887345436956625, 44.4285439467232], [6.89783261258001, 44.43704339945349], [6.908214697178771, 44.4456709059678], [6.918490127249155, 44.45442516699538], [6.9286573553491895, 44.4633048641767], [6.938714850331721, 44.47230866026205], [6.948661097574998, 44.481435199312855], [6.958494599210773, 44.49068310690589], [6.96821387434987, 44.500050990340306], [6.977817459305203, 44.5095374388473], [6.9873039078122, 44.51914102380264], [6.996671791246614, 44.52886029894174], [7.005919698839654, 44.53869380057751], [7.015046237890456, 44.54864004782079], [7.024050033975805, 44.558697542803316], [7.032929731157133, 44.56886477090335], [7.041683992184705, 44.57914020097374], [7.050311498699011, 44.5895222855725], [7.0588109514293045, 44.60000946119588], [7.0671810703892675, 44.61060014851382], [7.075420595069772, 44.62129275260775], [7.083528284628709, 44.63208566321083], [7.091502918077855, 44.642977254950424], [7.099343294466742, 44.653965887592875], [7.107048233063528, 44.665049906290534], [7.1146165735328, 44.67622764183095], [7.122047176110322, 44.687497410888255], [7.1293389217746785, 44.6988575162767], [7.136490712415792, 44.71030624720619], [7.1435014710003, 44.721841879539966], [7.150370141733745, 44.733462676054216], [7.157095690219583, 44.74516688669974], [7.163677103614948, 44.75695274886547], [7.17011339078319, 44.76881848764391], [7.17640358244314, 44.780762316098446], [7.1825467313150675, 44.79278243553244], [7.188541912263349, 44.80487703576013], [7.194388222435788, 44.8170442953792], [7.200084781399575, 44.82928238204511], [7.205630731273884, 44.841589452747016], [7.211025236859063, 44.853963654085355], [7.216267485762415, 44.866403122550906], [7.221356688520538, 44.878905984805485], [7.226292078718213, 44.89147035796402], [7.231072913103833, 44.90409434987813], [7.235698471701323, 44.91677605942107], [7.240168057918574, 44.92951357677402], [7.244480998652341, 44.942304983713726], [7.248636644389613, 44.95514835390136], [7.25263436930543, 44.9680417531726], [7.256473571357123, 44.98098323982895], [7.260153672374984, 44.99397086493012], [7.263674118149337, 45.00700267258754], [7.267034378513999, 45.02007670025892], [7.270233947426116, 45.033190979043766], [7.273272343042382, 45.04634353397995], [7.276149107791591, 45.05953238434107], [7.278863808443553, 45.07275554393477], [7.281416036174338, 45.08601102140185], [7.2838054066278355, 45.09929682051617], [7.286031559973645, 45.11261094048526], [7.2880941609612595, 45.12595137625161], [7.289992898970558, 45.13931611879467], [7.291727488058581, 45.15270315543337], [7.293297667002592, 45.16611047012923], [7.294703199339417, 45.179536043789994],
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
