kpbianco/gr86-cca-telemetry/docs/engineering/rvb22/current/mechanics/THERMAL_CONTACT_T03.scad

// Current construction:200 unbonded C110 leaves, each0.010..0.011mm; see FLEX_CONSTRUCTION_W02_T03.json.
// T02 coordinated candidate: thermal reevaluation required.
module foil_packet(){translate([0,27.9,0])rotate([90,0,0])linear_extrude(15.1)polygon(points=[[67.5, -2.327], [67.5, -0.127], [71.3, -0.127], [71.40781885436252, -0.13229680066058358], [71.51459935421774, -0.14813619155644653], [71.61931314497991, -0.17436563069457023], [71.72095177560159, -0.21073251423758466], [71.8185364105086, -0.2568866092168096], [71.91112725632156, -0.3123834264672003], [71.99783261258001, -0.3766885013009893], [72.0778174593052, -0.4491825406947978], [72.15031149869901, -0.52916738741999], [72.2146165735328, -0.6158727436784377], [72.2701133907832, -0.7084635894914025], [72.31626748576241, -0.8060482243984013], [72.35263436930542, -0.9076868550200916], [72.37886380844355, -1.012400645782259], [72.39470319933942, -1.1191811456374834], [72.39999999999999, -1.227], [72.39487815202365, -1.3330275069087165], [72.37956030505222, -1.438067637868891], [72.35418910578301, -1.5411422118219895], [72.31900082226262, -1.6412913518625305], [72.27432314365242, -1.7375824240446052], [72.22057212863925, -1.8291187224896746], [72.15824833090943, -1.9150478199160048], [72.08793213776713, -1.994569505825846], [72.01027836530604, -2.066943238426374], [71.92601016046679, -2.1314950408887503], [71.83591226676653, -2.187623777724227], [71.74082371641346, -2.234806752828848], [71.64163001686069, -2.2726045770652346], [71.53925490456152, -2.300665260052341], [71.43465174271914, -2.3187274880585806], [71.32879464313866, -2.326623057473113], [71.2005814175485, -2.32998043894255], [71.10143533452094, -2.3377834049017934], [71.00283350343949, -2.350764582230358], [70.90504618506925, -2.3688883904235123], [70.8083414076529, -2.3921051533827487], [70.71298423226331, -2.420351235574614], [70.61923602629022, -2.4535492164511146], [70.52735374704972, -2.4916081026542893], [70.43758923748254, -2.534423577422475], [70.35018853586998, -2.581878286515418], [70.26539120145998, -2.6338421598740327], [70.18342965785214, -2.69017276813329], [70.10452855594019, -2.750715713011612], [70.02890415816007, -2.8153050505054087], [69.9567637457299, -2.883763745729839], [69.88830505050534, -2.955904158160167], [69.82371571301162, -3.031528555940172], [69.7631727681333, -3.1104296578521233], [69.70684215987407, -3.1923912014599107], [69.65487828651533, -3.2771885358701187], [69.60742357742251, -3.3645892374824644], [69.56460810265428, -3.454353747049748], [69.52654921645117, -3.5462360262900696], [69.49335123557458, -3.639984232263409], [69.46510515338277, -3.735341407652838], [69.4418883904235, -3.8320461850692933], [69.42376458223035, -3.9298335034395655], [69.41078340490178, -4.028435334520958], [69.40298043894254, -4.127581417548563], [69.39999999999999, -4.241399788793378], [69.39999999999999, -9.227], [69.39962305747311, -9.25579464313863], [69.39551166173683, -9.412802511867461], [69.39249767137017, -9.470312874029457], [69.38017475321126, -9.626890395103587], [69.374155033616, -9.684164201245066], [69.35365436929659, -9.839882206562798], [69.34464542010576, -9.896762473162042], [69.31602320052177, -10.051194150494627], [69.30404971463885, -10.107524972694822], [69.26738439130463, -10.260247035549106], [69.25247918722222, -10.315874014481835], [69.20787125724048, -10.466467862299114], [69.19007518908685, -10.521238528281998], [69.137646919693, -10.669291393793058], [69.11700876525404, -10.723055624237448], [69.05690385869025, -10.868161704828948], [69.03348018571265, -10.920772135716533], [68.96586338534995, -11.062533705707772], [68.93971839649325, -11.113846135504243], [68.86477503528145, -11.251874636285603], [68.83598039214282, -11.301748421187552], [68.75391588462577, -11.435665526232635], [68.72255051132049, -11.483963965662385], [68.63358979060907, -11.613402617494723], [68.5997396574452, -11.659993328787014], [68.50412655869127, -11.784598745059107], [68.46788444653096, -11.829354026312698], [68.36588103859224, -11.948784672239759], [68.3273462845457, -11.991581852339715], [68.21923215167315, -12.105510376822783], [68.17851037682276, -12.146232151673171], [68.06458185233969, -12.254346284545711], [68.02178467223976, -12.292881038592228], [67.9023540263127, -12.394884446530959], [67.85759874505911, -12.431126558691263], [67.73299332878702, -12.526739657445193], [67.68640261749475, -12.560589790609049], [67.55696396566242, -12.649550511320477], [67.50866552623262, -12.680915884625781], [67.37474842118753, -12.762980392142826], [67.32487463628556, -12.79177503528148], [67.1868461355042, -12.866718396493267], [67.13553370570774, -12.892863385349957], [66.9937721357165, -12.960480185712656], [66.94116170482901, -12.983903858690207], [66.79605562423752, -13.04400876525401], [66.74229139379304, -13.064646919693004], [66.59423852828198, -13.11707518908686], [66.53946786229916, -13.134871257240471], [66.38887401448189, -13.179479187222215], [66.33324703554904, -13.194384391304654], [66.18052497269474, -13.231049714638866], [66.12419415049463, -13.243023200521767], [65.96976247316205, -13.271645420105763], [65.91288220656276, -13.280654369296604], [65.75716420124503, -13.301155033616011], [65.6998903951036, -13.30717475321126], [65.54331287402945, -13.319497671370163], [65.48580251186748, -13.322511661736836], [65.32879464313865, -13.326623057473114], [65.3, -13.327], [57.3, -13.327], [57.3, -11.127], [65.28560021120666, -11.127], [65.39941858245152, -11.12401956105745], [65.498564665479, -11.116216595098212], [65.59716649656053, -11.103235417769637], [65.69495381493076, -11.085111609576485], [65.7916585923471, -11.061894846617248], [65.88701576773667, -11.033648764425392], [65.98076397370978, -11.000450783548882], [66.0726462529503, -10.962391897345704], [66.1624107625175, -10.919576422577503], [66.24981146412995, -10.87212171348463], [66.33460879853999, -10.820157840125988], [66.4165703421479, -10.763827231866665], [66.49547144405982, -10.703284286988378], [66.57109584183986, -10.638694949494633], [66.64323625427006, -10.570236254270185], [66.71169494949473, -10.49809584183977], [66.77628428698836, -10.422471444059855], [66.83682723186669, -10.343570342147883], [66.89315784012592, -10.26160879854008], [66.94512171348467, -10.176811464129878], [66.99257642257753, -10.089410762517462], [67.03539189734565, -9.99964625295044], [67.07345078354886, -9.907763973709809], [67.1066487644254, -9.814015767736626], [67.13489484661723, -9.718658592347161], [67.1581116095765, -9.621953814930702], [67.17623541776965, -9.524166496560431], [67.18921659509822, -9.425564665479046], [67.19701956105746, -9.326418582451439], [67.2, -9.212600211206624], [67.2, -4.227], [67.20037694252689, -4.19820535686137], [67.20448833826316, -4.041197488132539], [67.20750232862983, -3.983687125970544], [67.21982524678873, -3.827109604896414], [67.22584496638399, -3.7698357987549334], [67.2463456307034, -3.6141177934372015], [67.25535457989423, -3.5572375268379597], [67.28397679947822, -3.402805849505375], [67.29595028536114, -3.346475027305181], [67.33261560869536, -3.193752964450896], [67.34752081277777, -3.1381259855181667], [67.39212874275951, -2.9875321377008874], [67.40992481091314, -2.9327614717179973], [67.462353080307, -2.784708606206939], [67.482991234746, -2.730944375762471], [67.5430961413098, -2.58583829517097], [67.56651981428732, -2.53322786428355], [67.63413661465, -2.391466294292311], [67.66028160350675, -2.340153864495755], [67.66742356920699, -2.327], [67.5, -2.327]]);}
color([.8,.4,.1])foil_packet();
color([1,1,1,.6])translate([67.5,12.8,-.127])cube([3.8,15.1,.127]);
