kpbianco/gr86-cca-telemetry/docs/engineering/rvb22/current/mechanics/THERMAL_LANDINGS_C04.scad

// Required cold terminal plates. Bolts clamp to the installed cold structure.
$fn=64;
color([.8,.4,.1]){difference(){translate([7.4, -9, -14.427])cube([54.1, 9, 2]);for(p=[[11, -4.6], [57.5, -4.6]])translate([p[0],p[1],-15.427])cylinder(d=3.4,h=4);}color("silver")translate([11, -4.6, -12.427])cylinder(d=6,h=2.4);color("silver")translate([57.5, -4.6, -12.427])cylinder(d=6,h=2.4);difference(){translate([7.4, 42, -14.427])cube([54.1, 9, 2]);for(p=[[11, 46.6], [57.5, 46.6]])translate([p[0],p[1],-15.427])cylinder(d=3.4,h=4);}color("silver")translate([11, 46.6, -12.427])cylinder(d=6,h=2.4);color("silver")translate([57.5, 46.6, -12.427])cylinder(d=6,h=2.4);difference(){translate([51, 4, -15.327])cube([15.5, 31.799999999999997, 2]);for(p=[[54, 7.5], [54, 32.3]])translate([p[0],p[1],-16.326999999999998])cylinder(d=3.4,h=4);}color("silver")translate([54, 7.5, -13.327])cylinder(d=6,h=2.4);color("silver")translate([54, 32.3, -13.327])cylinder(d=6,h=2.4);}
