kpbianco/gr86-cca-telemetry/docs/engineering/rvb22/current/mechanics/THERMAL_WING_W02.scad

// Current construction:200 unbonded C110 leaves, each0.010..0.011mm; see FLEX_CONSTRUCTION_W02_T03.json.
// W01:200 individually formed, unbonded C110 laminae. Envelope is0.010..0.011mm per leaf.
module upper_wing_packet(){translate([15,0,0])rotate([90,0,90])linear_extrude(38)polygon(points=[[-7.593250399826597, -2.327], [-7.636809809930994, -2.3275345812217823], [-7.673597447008879, -2.3288895501290074], [-7.710340751736667, -2.331146924753277], [-7.747017591321544, -2.3343053453365274], [-7.783605873006727, -2.3383629093642972], [-7.820083557379486, -2.343317172711741], [-7.856428671646745, -2.3491651511158707], [-7.892619322870653, -2.3559033219731575], [-7.92863371115625, -2.363527626461448], [-7.964450142782627, -2.372033471984797], [-8.000047043270657, -2.381415734939918], [-8.035402970378552, -2.391668763802436], [-8.070496627017858, -2.4027863825311493], [-8.105306874082066, -2.414761894288253], [-8.13981274317994, -2.427588085473244], [-8.173993449266225, -2.4412572300681656], [-8.207828403161658, -2.4557610942914283], [-8.241297223955229, -2.47109094155758], [-8.274379751280714, -2.487237537739823], [-8.307056057460752, -2.5041911567324067], [-8.339306459510231, -2.5219415863091266], [-8.371111530993002, -2.540478134275006], [-8.402452113723216, -2.559789634906644], [-8.433309329305695, -2.5798644556781385], [-8.463664590507681, -2.600690504268156], [-8.493499612454881, -2.6222552358437623], [-8.52279642364556, -2.644545660616928], [-8.551537376776295, -2.6675483516693856], [-8.579705159371473, -2.691249453040057], [-8.607282804212195, -2.715634688071782], [-8.63425369955642, -2.7406893680108113], [-8.660601599145243, -2.7663984008547593], [-8.686310631989178, -2.79274630044357], [-8.711365311928237, -2.8197171957878244], [-8.735750546959913, -2.8472948406284924], [-8.759451648330646, -2.8754626232237435], [-8.782454339383042, -2.9042035763544014], [-8.804744764156256, -2.9335003875451435], [-8.826309495731849, -2.9633354094923243], [-8.847135544321834, -2.9936906706942636], [-8.867210365093367, -3.024547886276805], [-8.886521865724982, -3.0558884690069785], [-8.905058413690897, -3.0876935404898123], [-8.922808843267601, -3.119943942539261], [-8.939762462260175, -3.1526202487192796], [-8.95590905844241, -3.185702776044749], [-8.971238905708555, -3.2191715968383057], [-8.985742769931834, -3.253006550733776], [-8.99941191452677, -3.287187256820095], [-9.012238105711742, -3.321693125917921], [-9.024213617468863, -3.3565033729821816], [-9.035331236197553, -3.3915970296214164], [-9.045584265060079, -3.4269529567293326], [-9.054966528015196, -3.4625498572173488], [-9.063472373538556, -3.4983662888437705], [-9.071096678026848, -3.534380677129374], [-9.077834848884127, -3.5705713283532425], [-9.083682827288253, -3.6069164426204807], [-9.088637090635702, -3.64339412699327], [-9.092694654663473, -3.679982408678473], [-9.095853075246724, -3.716659248263351], [-9.098110449870989, -3.7534025529910595], [-9.09946541877822, -3.7901901900690658], [-9.1, -3.8337496001733586], [-9.1, -8.720250399826641], [-9.09946541877822, -8.763809809930933], [-9.098110449870989, -8.800597447008945], [-9.095853075246726, -8.837340751736633], [-9.092694654663472, -8.874017591321541], [-9.088637090635704, -8.910605873006718], [-9.083682827288257, -8.947083557379493], [-9.077834848884129, -8.983428671646747], [-9.071096678026837, -9.01961932287068], [-9.063472373538549, -9.055633711156263], [-9.05496652801521, -9.091450142782595], [-9.04558426506007, -9.127047043270696], [-9.03533123619757, -9.162402970378533], [-9.024213617468854, -9.197496627017847], [-9.01223810571175, -9.23230687408205], [-8.99941191452673, -9.266812743180006], [-8.985742769931857, -9.300993449266173], [-8.971238905708567, -9.334828403161666], [-8.955909058442419, -9.368297223955228], [-8.939762462260152, -9.401379751280766], [-8.922808843267624, -9.434056057460696], [-8.905058413690869, -9.46630645951024], [-8.886521865724989, -9.498111530993013], [-8.867210365093362, -9.529452113723204], [-8.84713554432186, -9.560309329305696], [-8.826309495731818, -9.59066459050772], [-8.804744764156272, -9.620499612454836], [-8.782454339383051, -9.649796423645586], [-8.759451648330637, -9.678537376776267], [-8.73575054695992, -9.706705159371499], [-8.711365311928219, -9.734282804212194], [-8.686310631989212, -9.761253699556393], [-8.660601599145213, -9.78760159914527], [-8.634253699556403, -9.813310631989204], [-8.60728280421219, -9.838365311928223], [-8.57970515937152, -9.862750546959903], [-8.551537376776245, -9.886451648330656], [-8.522796423645573, -9.90945433938306], [-8.493499612454873, -9.931744764156244], [-8.4636645905077, -9.953309495731832], [-8.433309329305684, -9.97413554432187], [-8.402452113723216, -9.994210365093357], [-8.371111530993026, -10.01352186572498], [-8.339306459510192, -10.032058413690894], [-8.30705605746073, -10.049808843267606], [-8.274379751280724, -10.066762462260174], [-8.241297223955232, -10.082909058442418], [-8.207828403161704, -10.09823890570855], [-8.173993449266176, -10.112742769931854], [-8.139812743179988, -10.126411914526736], [-8.105306874082048, -10.139238105711753], [-8.070496627017816, -10.151213617468864], [-8.035402970378597, -10.16233123619755], [-8.000047043270662, -10.17258426506008], [-7.964450142782573, -10.181966528015217], [-7.928633711156272, -10.190472373538547], [-7.892619322870654, -10.198096678026843], [-7.856428671646747, -10.20483484888413], [-7.8200835573795136, -10.210682827288254], [-7.783605873006701, -10.215637090635706], [-7.747017591321516, -10.219694654663478], [-7.710340751736692, -10.222853075246723], [-7.67359744700894, -10.22511044987099], [-7.636809809930934, -10.22646541877822], [-7.593250399826641, -10.227], [-1.6, -10.227], [-1.6, -12.427], [-7.6000000000000005, -12.427], [-7.613498692114282, -12.426917172023058], [-7.677305886273854, -12.42613410063319], [-7.704295139395061, -12.425471551657317], [-7.768063898486775, -12.423122809180635], [-7.795028763183722, -12.421798110323612], [-7.85872067529157, -12.417885111554758], [-7.885644908938003, -12.415899060765652], [-7.9492216084357255, -12.41042416274877], [-7.976088992880145, -12.407777956350303], [-8.03951218354125, -12.400744456959236], [-8.066306534875823, -12.397439688927202], [-8.129538012941799, -12.388851824878985], [-8.15624319125116, -12.384890485882078], [-8.219244868444006, -12.374753430184896], [-8.245844787527451, -12.370137906385583], [-8.3085787139926, -12.358457765222735], [-8.335057351053361, -12.353190836839993], [-8.39748573821929, -12.339974645891768], [-8.423827143516615, -12.334059485526288], [-8.485912386857239, -12.319315205731927], [-8.512100693313458, -12.31275537645515], [-8.573805394999708, -12.29649188921748], [-8.599824827758292, -12.289291342425267], [-8.661111819185159, -12.271518444260867], [-8.686946705112756, -12.263681517293355], [-8.74777906928827, -12.244409913931507], [-8.773413846415611, -12.235941327460468], [-8.833754940198265, -12.215182627394427], [-8.859174167094146, -12.206087482579688], [-8.918987643265343, -12.183854190074156], [-8.944176008337978, -12.174137965490862], [-9.003425837496245, -12.150443473049886], [-9.028368168216405, -12.140112021388402], [-9.087018660480142, -12.114970601688237], [-9.111699932520366, -12.104030146228757], [-9.16971575902613, -12.077456943520529], [-9.194121105311112, -12.065914074384303], [-9.251467319494353, -12.03792509537169], [-9.275582039156031, -12.025786765551484], [-9.332224097801648, -11.996398869748868], [-9.356033665034644, -11.983672390920661], [-9.411937449084489, -11.952903280497587], [-9.435427521895715, -11.939596318616402], [-9.490559357000652, -11.907464527734462], [-9.513715785848694, -11.893585098416498], [-9.568042462652771, -11.860109982065028], [-9.590851298970694, -11.845666445759566], [-9.644340093115208, -11.810868168096945], [-9.666787597712952, -11.795869225050138], [-9.719406289548383, -11.759768747257638], [-9.741478940888479, -11.744223432271973], [-9.793195834882408, -11.706842499927532], [-9.814880337225086, -11.690760176919447], [-9.865664281054391, -11.652121306898945], [-9.88694757246624, -11.635511663258491], [-9.93676797578209, -11.595638130172432], [-9.957637236004263, -11.578511170927811], [-10.006464088858603, -11.537426993101555], [-10.026906747029006, -11.519793034892666], [-10.074710637951435, -11.4775229598987], [-10.094714380177248, -11.459392624762547], [-10.141466513891373, -11.415962114513468], [-10.161019290666246, -11.397346323486014], [-10.206691505434893, -11.352781538897224], [-10.225781538897223, -11.333691505434896], [-10.270346323486015, -11.288019290666245], [-10.288962114513469, -11.268466513891372], [-10.332392624762548, -11.221714380177247], [-10.350522959898703, -11.201710637951432], [-10.392793034892668, -11.153906747029005], [-10.410426993101566, -11.133464088858588], [-10.451511170927823, -11.084637236004246], [-10.468638130172417, -11.063767975782106], [-10.508511663258478, -11.013947572466257], [-10.52512130689895, -10.992664281054386], [-10.56376017691945, -10.941880337225083], [-10.579842499927521, -10.920195834882422], [-10.617223432271961, -10.868478940888496], [-10.632768747257657, -10.846406289548357], [-10.668869225050157, -10.793787597712923], [-10.683868168096945, -10.771340093115207], [-10.718666445759565, -10.717851298970693], [-10.733109982065018, -10.695042462652784], [-10.766585098416488, -10.640715785848709], [-10.780464527734448, -10.617559357000674], [-10.812596318616391, -10.562427521895737], [-10.825903280497602, -10.538937449084466], [-10.856672390920675, -10.483033665034622], [-10.869398869748867, -10.459224097801648], [-10.898786765551483, -10.402582039156032], [-10.910925095371685, -10.378467319494368], [-10.938914074384298, -10.321121105311123], [-10.950456943520532, -10.296715759026126], [-10.977030146228758, -10.238699932520367], [-10.987970601688234, -10.214018660480148], [-11.013112021388402, -10.155368168216407], [-11.02344347304989, -10.130425837496238], [-11.047137965490863, -10.071176008337975], [-11.056854190074155, -10.045987643265345], [-11.079087482579688, -9.986174167094148], [-11.08818262739443, -9.960754940198257], [-11.108941327460471, -9.900413846415601], [-11.117409913931501, -9.87477906928829], [-11.13668151729335, -9.813946705112775], [-11.144518444260873, -9.788111819185136], [-11.162291342425272, -9.726824827758271], [-11.16949188921748, -9.700805394999701], [-11.185755376455152, -9.63910069331345], [-11.192315205731926, -9.612912386857237], [-11.207059485526287, -9.550827143516614], [-11.212974645891768, -9.524485738219289], [-11.226190836839992, -9.46205735105336], [-11.231457765222736, -9.435578713992594], [-11.243137906385584, -9.372844787527443], [-11.24775343018489, -9.346244868444044], [-11.257890485882074, -9.283243191251202], [-11.261851824878992, -9.256538012941766], [-11.270439688927206, -9.193306534875788], [-11.273744456959239, -9.16651218354122], [-11.280777956350304, -9.103088992880116], [-11.283424162748766, -9.076221608435757], [-11.28889906076565, -9.012644908938036], [-11.290885111554758, -8.985720675291569], [-11.294798110323612, -8.92202876318372], [-11.296122809180634, -8.895063898486775], [-11.298471551657316, -8.83129513939506], [-11.29913410063319, -8.804305886273854], [-11.299917172023058, -8.740498692114283], [-11.299999999999999, -8.727], [-11.299999999999999, -3.8269999999999995], [-11.299917172023058, -3.813501307885718], [-11.29913410063319, -3.749694113726146], [-11.298471551657316, -3.722704860604939], [-11.296122809180634, -3.6589361015132247], [-11.294798110323612, -3.631971236816278], [-11.290885111554758, -3.56827932470843], [-11.28889906076565, -3.541355091061968], [-11.283424162748766, -3.477778391564245], [-11.280777956350304, -3.450911007119882], [-11.273744456959239, -3.3874878164587776], [-11.270439688927206, -3.3606934651242124], [-11.261851824878992, -3.297461987058234], [-11.257890485882074, -3.2707568087488013], [-11.24775343018489, -3.207755131555958], [-11.243137906385583, -3.18115521247255], [-11.231457765222734, -3.1184212860074], [-11.226190836839992, -3.091942648946637], [-11.212974645891768, -3.029514261780709], [-11.207059485526289, -3.003172856483388], [-11.192315205731928, -2.9410876131427637], [-11.18575537645515, -2.914899306686543], [-11.169491889217479, -2.853194605000293], [-11.162291342425265, -2.827175172241704], [-11.144518444260864, -2.765888180814838], [-11.136681517293356, -2.7400532948872507], [-11.117409913931509, -2.679220930711735], [-11.108941327460467, -2.653586153584389], [-11.088182627394426, -2.593245059801735], [-11.07908748257969, -2.5678258329058608], [-11.056854190074157, -2.5080123567346626], [-11.047137965490856, -2.4828239916620034], [-11.02344347304988, -2.4235741625037392], [-11.013112021388409, -2.3986318317836126], [-10.987970601688243, -2.3399813395198725], [-10.977030146228762, -2.3153000674796416], [-10.950456943520535, -2.257284240973881], [-10.938914074384295, -2.2328788946888705], [-10.910925095371681, -2.175532680505627], [-10.898786765551485, -2.1514179608439705], [-10.869398869748869, -2.0947759021983536], [-10.856672390920659, -2.070966334965351], [-10.825903280497585, -2.015062550915507], [-10.812596318616391, -1.9915724781042659], [-10.780464527734448, -1.936440642999328], [-10.766585098416503, -1.9132842141513158], [-10.733109982065034, -1.8589575373472398], [-10.718666445759563, -1.8361487010293014], [-10.683868168096943, -1.7826599068847884], [-10.668869225050146, -1.760212402287062], [-10.632768747257646, -1.7075937104516297], [-10.617223432271976, -1.6855210591115237], [-10.579842499927535, -1.6338041651175947], [-10.563760176919448, -1.612119662774913], [-10.525121306898948, -1.5613357189456099], [-10.508511663258474, -1.5400524275337375], [-10.468638130172414, -1.4902320242178893], [-10.451511170927823, -1.4693627639957532], [-10.410426993101566, -1.4205359111414113], [-10.392793034892655, -1.400093252970981], [-10.350522959898688, -1.3522893620485532], [-10.332392624762553, -1.3322856198227602], [-10.288962114513474, -1.2855334861086336], [-10.270346323486015, -1.2659807093337563], [-10.225781538897225, -1.2203084945651073], [-10.206691505434899, -1.2012184611027803], [-10.16101929066625, -1.15665367651399], [-10.141466513891361, -1.1380378854865203], [-10.094714380177233, -1.094607375237441], [-10.074710637951442, -1.0764770401013073], [-10.026906747029015, -1.0342069651073413], [-10.00646408885859, -1.0165730068984353], [-9.957637236004247, -0.9754888290721786], [-9.936767975782102, -0.9583618698275786], [-9.886947572466253, -0.9184883367415184], [-9.865664281054395, -0.9018786931010575], [-9.814880337225093, -0.8632398230805572], [-9.7931958348824, -0.8471575000724615], [-9.74147894088847, -0.8097765677280205], [-9.719406289548374, -0.7942312527423563], [-9.666787597712942, -0.7581307749498558], [-9.644340093115225, -0.7431318319030668], [-9.590851298970714, -0.708333554240446], [-9.568042462652755, -0.6938900179349612], [-9.513715785848678, -0.6604149015834926], [-9.490559357000668, -0.6465354722655491], [-9.43542752189573, -0.6144036813836068], [-9.411937449084471, -0.601096719502402], [-9.356033665034627, -0.5703276090793288], [-9.332224097801655, -0.5576011302511357], [-9.275582039156038, -0.5282132344485193], [-9.251467319494367, -0.5160749046283154], [-9.194121105311122, -0.48808592561570163], [-9.169715759026133, -0.47654305647947126], [-9.111699932520374, -0.44996985377124465], [-9.08701866048012, -0.43902939831175436], [-9.02836816821638, -0.41388797861158855], [-9.003425837496257, -0.4035565269501187], [-8.944176008337994, -0.37986203450914324], [-8.918987643265341, -0.3701458099258441], [-8.859174167094142, -0.34791251742031104], [-8.833754940198265, -0.33881737260557365], [-8.773413846415611, -0.31805867253953224], [-8.747779069288269, -0.30959008606849125], [-8.686946705112753, -0.2903184827066434], [-8.661111819185157, -0.28248155573913336], [-8.599824827758292, -0.2647086575747333], [-8.5738053949997, -0.25750811078251856], [-8.51210069331345, -0.24124462354484755], [-8.48591238685723, -0.23468479426807054], [-8.423827143516606, -0.21994051447371055], [-8.397485738219295, -0.21402535410823353], [-8.335057351053367, -0.20080916316000885], [-8.308578713992592, -0.1955422347772635], [-8.245844787527442, -0.1838620936144153], [-8.219244868444028, -0.17924656981510756], [-8.156243191251184, -0.1691095141179244], [-8.12953801294178, -0.16514817512101154], [-8.0663065348758, -0.156560311072796], [-8.039512183541238, -0.15325554304076272], [-7.9760889928801335, -0.1462220436496966], [-7.9492216084357326, -0.14357583725123102], [-7.88564490893801, -0.13810093923434885], [-7.85872067529157, -0.1361148884452419], [-7.795028763183722, -0.1322018896763879], [-7.7680638984867825, -0.1308771908193671], [-7.704295139395067, -0.1285284483426843], [-7.677305886273857, -0.1278658993668096], [-7.613498692114285, -0.12708282797694093], [-7.6, -0.127], [-1.6, -0.127], [-1.6, -2.327], [-7.593250399826597, -2.327]]);}
module lower_wing_packet(){translate([15,0,0])rotate([90,0,90])linear_extrude(38)polygon(points=[[49.593250399826594, -2.327], [49.636809809930995, -2.3275345812217823], [49.67359744700888, -2.3288895501290074], [49.710340751736666, -2.331146924753277], [49.747017591321544, -2.3343053453365274], [49.78360587300673, -2.3383629093642972], [49.82008355737948, -2.343317172711741], [49.856428671646746, -2.3491651511158707], [49.89261932287065, -2.3559033219731575], [49.92863371115625, -2.363527626461448], [49.964450142782624, -2.372033471984797], [50.000047043270655, -2.381415734939918], [50.035402970378556, -2.391668763802436], [50.07049662701786, -2.4027863825311493], [50.10530687408207, -2.414761894288253], [50.13981274317994, -2.427588085473244], [50.17399344926623, -2.4412572300681656], [50.207828403161656, -2.4557610942914283], [50.24129722395523, -2.47109094155758], [50.27437975128071, -2.487237537739823], [50.307056057460755, -2.5041911567324067], [50.33930645951023, -2.5219415863091266], [50.371111530993005, -2.540478134275006], [50.402452113723214, -2.559789634906644], [50.43330932930569, -2.5798644556781385], [50.46366459050768, -2.600690504268156], [50.49349961245488, -2.6222552358437623], [50.52279642364556, -2.644545660616928], [50.551537376776295, -2.6675483516693856], [50.57970515937147, -2.691249453040057], [50.6072828042122, -2.715634688071782], [50.63425369955642, -2.7406893680108113], [50.660601599145245, -2.7663984008547593], [50.68631063198918, -2.79274630044357], [50.71136531192823, -2.8197171957878244], [50.73575054695991, -2.8472948406284924], [50.759451648330646, -2.8754626232237435], [50.782454339383044, -2.9042035763544014], [50.804744764156254, -2.9335003875451435], [50.82630949573185, -2.9633354094923243], [50.84713554432183, -2.9936906706942636], [50.86721036509337, -3.024547886276805], [50.88652186572498, -3.0558884690069785], [50.905058413690895, -3.0876935404898123], [50.9228088432676, -3.119943942539261], [50.93976246226018, -3.1526202487192796], [50.95590905844241, -3.185702776044749], [50.97123890570855, -3.2191715968383057], [50.98574276993183, -3.253006550733776], [50.99941191452677, -3.287187256820095], [51.012238105711745, -3.321693125917921], [51.02421361746886, -3.3565033729821816], [51.03533123619755, -3.3915970296214164], [51.04558426506008, -3.4269529567293326], [51.0549665280152, -3.4625498572173488], [51.06347237353856, -3.4983662888437705], [51.07109667802685, -3.534380677129374], [51.07783484888412, -3.5705713283532425], [51.08368282728826, -3.6069164426204807], [51.0886370906357, -3.64339412699327], [51.092694654663475, -3.679982408678473], [51.09585307524672, -3.716659248263351], [51.09811044987099, -3.7534025529910595], [51.09946541877822, -3.7901901900690658], [51.1, -3.8337496001733586], [51.1, -8.720250399826641], [51.09946541877822, -8.763809809930933], [51.09811044987099, -8.800597447008945], [51.09585307524672, -8.837340751736633], [51.092694654663475, -8.874017591321541], [51.0886370906357, -8.910605873006718], [51.08368282728826, -8.947083557379493], [51.07783484888413, -8.983428671646747], [51.071096678026834, -9.01961932287068], [51.063472373538545, -9.055633711156263], [51.054966528015214, -9.091450142782595], [51.04558426506007, -9.127047043270696], [51.03533123619757, -9.162402970378533], [51.02421361746885, -9.197496627017847], [51.01223810571175, -9.23230687408205], [50.99941191452673, -9.266812743180006], [50.98574276993186, -9.300993449266173], [50.97123890570857, -9.334828403161666], [50.955909058442415, -9.368297223955228], [50.93976246226015, -9.401379751280766], [50.922808843267624, -9.434056057460696], [50.90505841369087, -9.46630645951024], [50.88652186572499, -9.498111530993013], [50.867210365093364, -9.529452113723204], [50.84713554432186, -9.560309329305696], [50.82630949573182, -9.59066459050772], [50.80474476415627, -9.620499612454836], [50.78245433938305, -9.649796423645586], [50.75945164833064, -9.678537376776267], [50.73575054695992, -9.706705159371499], [50.71136531192822, -9.734282804212194], [50.686310631989215, -9.761253699556393], [50.66060159914521, -9.78760159914527], [50.6342536995564, -9.813310631989204], [50.60728280421219, -9.838365311928223], [50.57970515937152, -9.862750546959903], [50.551537376776245, -9.886451648330656], [50.52279642364557, -9.90945433938306], [50.49349961245487, -9.931744764156244], [50.4636645905077, -9.953309495731832], [50.433309329305686, -9.97413554432187], [50.402452113723214, -9.994210365093357], [50.371111530993026, -10.01352186572498], [50.33930645951019, -10.032058413690894], [50.30705605746073, -10.049808843267606], [50.274379751280726, -10.066762462260174], [50.24129722395523, -10.082909058442418], [50.207828403161706, -10.09823890570855], [50.17399344926618, -10.112742769931854], [50.13981274317999, -10.126411914526736], [50.105306874082046, -10.139238105711753], [50.07049662701782, -10.151213617468864], [50.0354029703786, -10.16233123619755], [50.00004704327066, -10.17258426506008], [49.964450142782574, -10.181966528015217], [49.92863371115627, -10.190472373538547], [49.89261932287065, -10.198096678026843], [49.856428671646746, -10.20483484888413], [49.82008355737951, -10.210682827288254], [49.7836058730067, -10.215637090635706], [49.747017591321516, -10.219694654663478], [49.710340751736695, -10.222853075246723], [49.67359744700894, -10.22511044987099], [49.63680980993094, -10.22646541877822], [49.593250399826644, -10.227], [43.6, -10.227], [43.6, -12.427], [49.6, -12.427], [49.613498692114284, -12.426917172023058], [49.67730588627386, -12.42613410063319], [49.70429513939506, -12.425471551657317], [49.76806389848677, -12.423122809180635], [49.79502876318372, -12.421798110323612], [49.85872067529157, -12.417885111554758], [49.885644908938005, -12.415899060765652], [49.94922160843573, -12.41042416274877], [49.97608899288014, -12.407777956350303], [50.03951218354125, -12.400744456959236], [50.06630653487582, -12.397439688927202], [50.1295380129418, -12.388851824878985], [50.156243191251164, -12.384890485882078], [50.21924486844401, -12.374753430184896], [50.24584478752745, -12.370137906385583], [50.3085787139926, -12.358457765222735], [50.335057351053365, -12.353190836839993], [50.39748573821929, -12.339974645891768], [50.42382714351662, -12.334059485526288], [50.48591238685724, -12.319315205731927], [50.51210069331346, -12.31275537645515], [50.57380539499971, -12.29649188921748], [50.59982482775829, -12.289291342425267], [50.66111181918516, -12.271518444260867], [50.68694670511276, -12.263681517293355], [50.74777906928827, -12.244409913931507], [50.77341384641561, -12.235941327460468], [50.83375494019826, -12.215182627394427], [50.859174167094146, -12.206087482579688], [50.91898764326534, -12.183854190074156], [50.944176008337976, -12.174137965490862], [51.003425837496245, -12.150443473049886], [51.0283681682164, -12.140112021388402], [51.08701866048014, -12.114970601688237], [51.11169993252037, -12.104030146228757], [51.16971575902613, -12.077456943520529], [51.19412110531111, -12.065914074384303], [51.25146731949435, -12.03792509537169], [51.275582039156035, -12.025786765551484], [51.33222409780165, -11.996398869748868], [51.356033665034644, -11.983672390920661], [51.41193744908449, -11.952903280497587], [51.43542752189572, -11.939596318616402], [51.49055935700065, -11.907464527734462], [51.513715785848696, -11.893585098416498], [51.56804246265277, -11.860109982065028], [51.59085129897069, -11.845666445759566], [51.644340093115204, -11.810868168096945], [51.666787597712954, -11.795869225050138], [51.71940628954838, -11.759768747257638], [51.74147894088848, -11.744223432271973], [51.79319583488241, -11.706842499927532], [51.814880337225084, -11.690760176919447], [51.86566428105439, -11.652121306898945], [51.88694757246624, -11.635511663258491], [51.93676797578209, -11.595638130172432], [51.95763723600426, -11.578511170927811], [52.00646408885861, -11.537426993101555], [52.026906747029, -11.519793034892666], [52.07471063795143, -11.4775229598987], [52.09471438017725, -11.459392624762547], [52.14146651389137, -11.415962114513468], [52.161019290666246, -11.397346323486014], [52.20669150543489, -11.352781538897224], [52.22578153889722, -11.333691505434896], [52.27034632348602, -11.288019290666245], [52.28896211451347, -11.268466513891372], [52.33239262476255, -11.221714380177247], [52.350522959898704, -11.201710637951432], [52.39279303489267, -11.153906747029005], [52.41042699310157, -11.133464088858588], [52.45151117092782, -11.084637236004246], [52.468638130172415, -11.063767975782106], [52.508511663258474, -11.013947572466257], [52.52512130689895, -10.992664281054386], [52.56376017691945, -10.941880337225083], [52.57984249992752, -10.920195834882422], [52.61722343227196, -10.868478940888496], [52.63276874725766, -10.846406289548357], [52.66886922505016, -10.793787597712923], [52.68386816809694, -10.771340093115207], [52.71866644575957, -10.717851298970693], [52.73310998206502, -10.695042462652784], [52.766585098416485, -10.640715785848709], [52.78046452773445, -10.617559357000674], [52.81259631861639, -10.562427521895737], [52.8259032804976, -10.538937449084466], [52.85667239092068, -10.483033665034622], [52.86939886974886, -10.459224097801648], [52.898786765551485, -10.402582039156032], [52.91092509537168, -10.378467319494368], [52.9389140743843, -10.321121105311123], [52.950456943520535, -10.296715759026126], [52.977030146228756, -10.238699932520367], [52.98797060168823, -10.214018660480148], [53.0131120213884, -10.155368168216407], [53.02344347304989, -10.130425837496238], [53.04713796549086, -10.071176008337975], [53.056854190074155, -10.045987643265345], [53.07908748257969, -9.986174167094148], [53.08818262739443, -9.960754940198257], [53.10894132746047, -9.900413846415601], [53.1174099139315, -9.87477906928829], [53.136681517293354, -9.813946705112775], [53.144518444260875, -9.788111819185136], [53.16229134242527, -9.726824827758271], [53.16949188921748, -9.700805394999701], [53.18575537645515, -9.63910069331345], [53.19231520573193, -9.612912386857237], [53.20705948552629, -9.550827143516614], [53.21297464589177, -9.524485738219289], [53.22619083683999, -9.46205735105336], [53.231457765222736, -9.435578713992594], [53.243137906385584, -9.372844787527443], [53.247753430184886, -9.346244868444044], [53.25789048588207, -9.283243191251202], [53.26185182487899, -9.256538012941766], [53.270439688927205, -9.193306534875788], [53.273744456959236, -9.16651218354122], [53.280777956350306, -9.103088992880116], [53.283424162748766, -9.076221608435757], [53.28889906076565, -9.012644908938036], [53.29088511155476, -8.985720675291569], [53.29479811032361, -8.92202876318372], [53.29612280918063, -8.895063898486775], [53.298471551657315, -8.83129513939506], [53.29913410063319, -8.804305886273854], [53.29991717202306, -8.740498692114283], [53.3, -8.727], [53.3, -3.8269999999999995], [53.29991717202306, -3.813501307885718], [53.29913410063319, -3.749694113726146], [53.298471551657315, -3.722704860604939], [53.29612280918063, -3.6589361015132247], [53.29479811032361, -3.631971236816278], [53.29088511155476, -3.56827932470843], [53.28889906076565, -3.541355091061968], [53.283424162748766, -3.477778391564245], [53.280777956350306, -3.450911007119882], [53.273744456959236, -3.3874878164587776], [53.270439688927205, -3.3606934651242124], [53.26185182487899, -3.297461987058234], [53.25789048588207, -3.2707568087488013], [53.247753430184886, -3.207755131555958], [53.243137906385584, -3.18115521247255], [53.231457765222736, -3.1184212860074], [53.22619083683999, -3.091942648946637], [53.21297464589177, -3.029514261780709], [53.20705948552629, -3.003172856483388], [53.19231520573193, -2.9410876131427637], [53.18575537645515, -2.914899306686543], [53.16949188921748, -2.853194605000293], [53.16229134242526, -2.827175172241704], [53.14451844426087, -2.765888180814838], [53.136681517293354, -2.7400532948872507], [53.11740991393151, -2.679220930711735], [53.10894132746047, -2.653586153584389], [53.088182627394424, -2.593245059801735], [53.07908748257969, -2.5678258329058608], [53.056854190074155, -2.5080123567346626], [53.047137965490855, -2.4828239916620034], [53.02344347304988, -2.4235741625037392], [53.01311202138841, -2.3986318317836126], [52.98797060168825, -2.3399813395198725], [52.97703014622876, -2.3153000674796416], [52.950456943520535, -2.257284240973881], [52.93891407438429, -2.2328788946888705], [52.91092509537168, -2.175532680505627], [52.898786765551485, -2.1514179608439705], [52.86939886974887, -2.0947759021983536], [52.85667239092066, -2.070966334965351], [52.825903280497585, -2.015062550915507], [52.81259631861639, -1.9915724781042659], [52.78046452773445, -1.936440642999328], [52.7665850984165, -1.9132842141513158], [52.73310998206503, -1.8589575373472398], [52.71866644575957, -1.8361487010293014], [52.68386816809694, -1.7826599068847884], [52.668869225050145, -1.760212402287062], [52.63276874725764, -1.7075937104516297], [52.61722343227198, -1.6855210591115237], [52.57984249992754, -1.6338041651175947], [52.563760176919445, -1.612119662774913], [52.525121306898946, -1.5613357189456099], [52.508511663258474, -1.5400524275337375], [52.468638130172415, -1.4902320242178893], [52.45151117092782, -1.4693627639957532], [52.41042699310157, -1.4205359111414113], [52.392793034892655, -1.400093252970981], [52.35052295989869, -1.3522893620485532], [52.332392624762555, -1.3322856198227602], [52.288962114513474, -1.2855334861086336], [52.27034632348602, -1.2659807093337563], [52.22578153889722, -1.2203084945651073], [52.2066915054349, -1.2012184611027803], [52.161019290666246, -1.15665367651399], [52.14146651389136, -1.1380378854865203], [52.09471438017724, -1.094607375237441], [52.07471063795144, -1.0764770401013073], [52.02690674702902, -1.0342069651073413], [52.00646408885859, -1.0165730068984353], [51.957637236004246, -0.9754888290721786], [51.936767975782104, -0.9583618698275786], [51.886947572466255, -0.9184883367415184], [51.86566428105439, -0.9018786931010575], [51.81488033722509, -0.8632398230805572], [51.7931958348824, -0.8471575000724615], [51.74147894088847, -0.8097765677280205], [51.719406289548374, -0.7942312527423563], [51.66678759771294, -0.7581307749498558], [51.644340093115225, -0.7431318319030668], [51.59085129897071, -0.708333554240446], [51.568042462652755, -0.6938900179349612], [51.513715785848674, -0.6604149015834926], [51.49055935700067, -0.6465354722655491], [51.43542752189573, -0.6144036813836068], [51.41193744908447, -0.601096719502402], [51.35603366503463, -0.5703276090793288], [51.33222409780166, -0.5576011302511357], [51.275582039156035, -0.5282132344485193], [51.25146731949437, -0.5160749046283154], [51.194121105311126, -0.48808592561570163], [51.16971575902613, -0.47654305647947126], [51.111699932520374, -0.44996985377124465], [51.08701866048012, -0.43902939831175436], [51.02836816821638, -0.41388797861158855], [51.00342583749626, -0.4035565269501187], [50.94417600833799, -0.37986203450914324], [50.91898764326534, -0.3701458099258441], [50.85917416709414, -0.34791251742031104], [50.83375494019826, -0.33881737260557365], [50.77341384641561, -0.31805867253953224], [50.74777906928827, -0.30959008606849125], [50.68694670511275, -0.2903184827066434], [50.66111181918516, -0.28248155573913336], [50.59982482775829, -0.2647086575747333], [50.5738053949997, -0.25750811078251856], [50.51210069331345, -0.24124462354484755], [50.48591238685723, -0.23468479426807054], [50.423827143516604, -0.21994051447371055], [50.397485738219295, -0.21402535410823353], [50.335057351053365, -0.20080916316000885], [50.30857871399259, -0.1955422347772635], [50.245844787527446, -0.1838620936144153], [50.21924486844403, -0.17924656981510756], [50.156243191251185, -0.1691095141179244], [50.12953801294178, -0.16514817512101154], [50.0663065348758, -0.156560311072796], [50.039512183541234, -0.15325554304076272], [49.976088992880136, -0.1462220436496966], [49.949221608435735, -0.14357583725123102], [49.88564490893801, -0.13810093923434885], [49.85872067529157, -0.1361148884452419], [49.79502876318372, -0.1322018896763879], [49.76806389848678, -0.1308771908193671], [49.704295139395064, -0.1285284483426843], [49.67730588627386, -0.1278658993668096], [49.613498692114284, -0.12708282797694093], [49.6, -0.127], [43.6, -0.127], [43.6, -2.327], [49.593250399826594, -2.327]]);}
color([.8,.4,.1]){upper_wing_packet();lower_wing_packet();}
