kpbianco/gr86-cca-telemetry/docs/engineering/rvb22/candidate/verification/populated_envelopes/FOIL_CORRECTION_STUDY.png

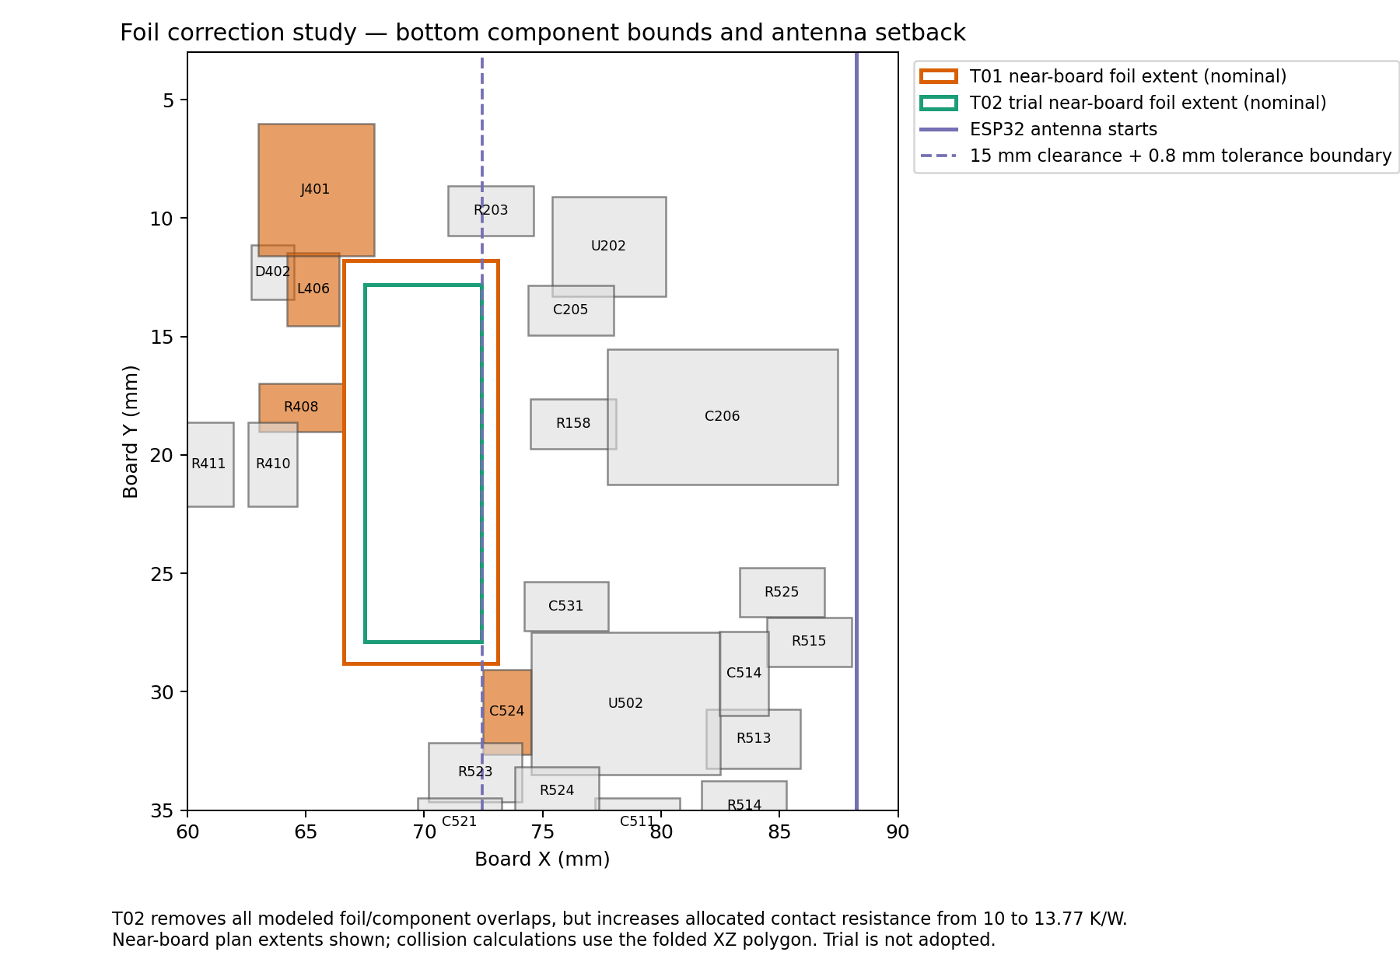
docs/engineering/rvb22/candidate/verification/populated_envelopes/FOIL_CORRECTION_STUDY.png
