kpbianco/gr86-cca-telemetry/docs/engineering/rvb22/candidate/firmware/cca_telemetry/config.h

#pragma once


// Customize your BLE device name here
#define DEVICE_NAME "CAN Telemetry"

// Runtime identity is BUILD_ID in the sketch. Exact reconstructed file hashes
// are recorded in SOURCE_MANIFEST.json; no historical commit is claimed.

// GPS PPS discipline (set to -1 to disable)
#define GPS_PPS_GPIO 16

// Default divider for RaceChronoPidMap extra (only used as init)
#define DEFAULT_UPDATE_RATE_DIVIDER 10

// Enable NVS-backed configuration persistence helpers
#define ENABLE_CCA_CFG_NVS 1

// CAN bus baud rate (500 kbps)
static const long BAUD_RATE = 500 * 1000L;

// ---- Car profile selection ----
#include "pidmaps/pidmap_defs.h"
#include "pidmaps/gr86_2022.h"

static constexpr const pidmaps::PidMapDefinition *ACTIVE_PID_MAP = &pidmaps::GR86_2022;
