kpbianco/gr86-cca-telemetry/docs/engineering/rvb22/candidate/firmware/cca_telemetry/src/gps_nmea.h

#pragma once

#include <cstddef>
#include <cstdint>

namespace gps {

constexpr std::size_t kMaxSentenceLength = 120;
constexpr int kMaxFields = 20;

struct RmcData {
  bool has_time = false;
  int hour = 0;
  int minute = 0;
  int second = 0;
  int millis = 0;
  bool valid = false;
  bool has_latitude = false;
  double latitude_deg = 0.0;
  bool has_longitude = false;
  double longitude_deg = 0.0;
  double speed_kmh = 0.0;
  double course_deg = 0.0;
  bool has_date = false;
  int day = 0;
  int month = 0;
  int year = 0;
};

struct GgaData {
  int fix_quality = 0;
  bool has_sats = false;
  int sats = 0;
  bool has_hdop = false;
  double hdop = 0.0;
  bool has_altitude = false;
  double altitude_m = 0.0;
};

bool parseRmcSentence(char *line, RmcData &out);
bool parseGgaSentence(char *line, GgaData &out);
// Accept only a bounded, checksum-valid NMEA sentence.
bool checksumOk(const char *line, std::size_t len);
// PA1616D v0.6 current antenna diagnostic: 1=internal, 2=external, 3=short.
bool parseAntennaStatus(const char *line, uint8_t &status);
bool parsePmtkAck(const char *line, uint16_t &command, uint8_t &result);

}  // namespace gps
